anand2532/nRF9161-DEV-BOARD/reports/PASS30Z_SUMMARY.md

# PASS30Z_SUMMARY — RF Class C only

**Timestamp:** 2026-09-23 13:23 IST
**Decision:** **KEEP**
**Phase:** COMPLETE_KEEP

## DRC

| | unconnected | shorting | clearance | crossing |
| --- | ---: | ---: | ---: | ---: |
| Before | 67 | 0 | 0 | 0 |
| After | 64 | 0 | 0 | 0 |

**Gate:** clean=True; unconnected 67→64; closed={'ANT_FIT': True, 'AUX': True, 'AUX_FIT': True}; protect=True

## Class C (ANT_FIT / AUX / AUX_FIT)

| Net | Before open? | After open? | Closed? |
| --- | --- | --- | --- |
| ANT_FIT | True | False | True |
| AUX | True | False | True |
| AUX_FIT | True | False | True |

## Final XY (C22/C23/C24)

| Ref | Final XY | Stub len (mm) | GND via |
| --- | --- | --- | --- |
| C22 | [17.5, 31.75] | 0.883 | [17.5, 32.23] |
| C23 | [24.8, 34.0] | 1.0 | [25.98, 34.0] |
| C24 | [15.0, 31.8] | 1.2 | [16.18, 31.8] |

## Protect checklist

```
{
  "stage_a": {
    "VDD_nRF_via_north": true,
    "VDD2_vias": 2,
    "VDD2_present": true
  },
  "p015_west_tracks": 21,
  "U1": [
    36.0,
    32.0
  ],
  "J13": [
    64.0,
    76.0
  ],
  "J10": [
    116.0,
    28.0
  ],
  "J11": [
    116.0,
    46.0
  ],
  "L1": [
    22.0,
    32.0
  ],
  "L2": [
    20.0,
    33.0
  ],
  "TP1": [
    12.0,
    33.0
  ],
  "J2": [
    8.0,
    32.0
  ],
  "J3": [
    8.0,
    40.0
  ],
  "U3": [
    26.5,
    47.0
  ],
  "FB5": [
    23.8,
    47.65
  ],
  "C27": [
    22.0,
    35.0
  ],
  "L4": [
    18.0,
    38.0
  ],
  "ok": true,
  "reasons": []
}
```

## Notes

Removed 3 old island stubs. Targets per RF_STUB_DNP_PLAN. Collisions: []

**Backup:** `/workspace/kicad-projects/nRF9161-DEV-BOARD/.mcp-backups/pass30z-rf-class-c/pre-edit.kicad_pcb`
**Script:** `scripts/final_pass30z.py`
**DRC:** `reports/DRC_PASS30Z_BEFORE.json`, `reports/DRC_PASS30Z_AFTER.json`
