anand2532/nRF9161-DEV-BOARD/docs/PCB_LAYOUT_REVIEW.md

# PCB Layout Review — nRF9161-DEV-BOARD

**Role:** PCB Layout Engineer  
**Working path:** `/workspace/kicad-projects/nRF9161-DEV-BOARD`  
**Review date:** 2026-09-30 12:43 IST (Asia/Calcutta) — pass30ax P0.16 KEEP (6-seg In1.Cu east skirt, no new via, foreign 0.21 mm, POWER 0.3378 mm; unc 60→59; P0.16 opens 1→0; GND islands 12→12 waived). Prior: 2026-09-30 11:27 IST (Asia/Calcutta) — pass30at P0.30 leftover NO-ROUTE (U1.88 via island to locked pass30as track 64.776 mm > 25 mm; no copper; unc 60). Prior: 2026-09-30 11:23 IST (Asia/Calcutta) — pass30as P0.30 KEEP (8-seg F.Cu+B.Cu jog, one via (112.40, 46.40), foreign 0.29 mm, POWER 0.7 mm; unc 61→60; P0.30 opens 2→1; GND islands 12→12 waived). Prior: 2026-09-30 11:07 IST (Asia/Calcutta) — pass30ar NO-ROUTE (P0.31 U1.89 to locked pass30aq track 66.737 mm > 25 mm; no copper; unc 61). Prior: 2026-09-30 11:01 IST (Asia/Calcutta) — pass30aq P0.31 KEEP (6-seg F.Cu jog around P0.22/P0.04/VDD_GPIO/J14, no via, foreign 0.23 mm, POWER 0.245 mm; unc 62→61; P0.31 opens 2→1; GND islands 12→12 waived). Prior: 2026-09-30 10:47 IST (Asia/Calcutta) — pass30ap VDD_GPIO last open KEEP (8-seg F.Cu jog around ENABLE/SIM_CLK/P0.20, no new via, POWER clearance 2.2373 mm; unc 63→62; VDD_GPIO opens 1→0; GND islands 12→12 waived). Prior: 2026-09-30 10:37 IST (Asia/Calcutta) — pass30ao NO-ROUTE (remaining VDD_GPIO 27.034 mm > 25 mm; shortest other `P0.31` 29.078 mm > 20 mm; unc 63→63, no copper). Prior: 2026-09-30 10:33 IST (Asia/Calcutta) — pass30an VDD_GPIO east KEEP (y=7.050, D3.1 clearance 0.385 mm; unc 63→63; VDD_GPIO opens 2→1; GND islands 11→12 waived). Prior: 2026-09-30 10:28 IST (Asia/Calcutta) — pass30am VDD_GPIO east REVERT (attempt mid: VDD_GPIO opens 2→1, clearance 1 vs D3.1 VIN, GND islands 11→12 waived; restored unc 63→63). Prior: pass30al COEX0 KEEP (unc 64→63; COEX0 opens 1→0; GND islands 11→11). Prior: pass30ak VDD_GPIO shove KEEP (unc headline was 64; VDD_GPIO opens 3→2; GND island 10→11 waived). Prior: pass30aj same geometry REVERT; pass30ac Package A REVERTED; SE column FROZEN (pass30z keep)
**Overall:** **NOT FABRICATION-READY** — connectivity hard gate open  
**Gerbers:** **Do not generate** until `unconnected_items = 0` and DFM checklist is green  

Cross-refs: `docs/FAB_READY_CHECKLIST.md` (DFM gate **RED**), `docs/FAB_STACKUP_NOTES.md`, `docs/PM_STATUS.md`, `reports/FINAL_FAB_RELEASE.md`, `reports/DRC_AFTER_CONNECT.json`, `reports/UNCONNECTED_AFTER_FINAL.csv`.

---

## 1. Current connectivity status

**2026-09-30 pass30ax:** P0.16 **KEEP**. Unconnected 60→59. P0.16 opens 1→0. See `reports/PASS30AX_SUMMARY.md`.

**2026-09-30 12:27 IST — pass30aw no-copper census.** U1-open pads 37, can exit 31, trapped 6 (U1.24 included). Board file not modified. See `reports/PASS30AW_SHORTLIST.md`.

| Metric | Count | Source |
| --- | --- | --- |
| **unconnected_items** | **59** | `reports/DRC_PASS30AX_AFTER.json`. pass30ax KEEP: P0.16 opens 1→0. Prior live count was 60 (`DRC_PASS30AS_AFTER.json`). pass30at NO-ROUTE (P0.30 leftover 64.776 mm > 25 mm, no copper). Prior pass30as KEEP: P0.30 opens 2→1. GND islands 12 (waived). foreign 0.29 mm, POWER 0.7 mm. Prior pass30ar NO-ROUTE
| **shorting_items** | **0** | `reports/DRC_PASS30AS_AFTER.json` |
| **clearance** | **0** | Pass30 after (was 6 at baseline; zone refill cleared via/zone hits) |
| **hole_clearance** | **0** | Same |
| via_dangling | **78** | `DRC_PASS30F_AFTER.json` |
| drill_out_of_range | **0** | Pass30 before/after — P0.02 & nRESET already ≥0.50/0.30 |
| via_diameter | **0** | Same |
| track_dangling | 13 | Same JSON (includes load-bearing P0.15 west-wrap stubs) |
| silk_overlap / silk_over_copper | 147 / 36 | Cosmetics — after copper freeze |
| Live copper | ~780 segments, ~250 vias | Live after pass30 |

### Count reconciliation (do not mix eras)

| Report | unconnected | Notes |
| --- | --- | --- |
| `reports/DRC_SUMMARY.txt` | 116 | Older summary — **superseded** |
| `reports/DRC_BEFORE_FINAL.json` | 120 | Pre-final pass |
| `reports/DRC_final.json` / `FINAL_DESIGN_REVIEW.md` | 104 | Mid campaign |
| `reports/DRC_AFTER_CONNECT_FULL.json` | 98 | Intermediate |
| **`DRC_PASS30W_AFTER.json`** | **67** | **Authoritative after pass30w** (STOP two fails; Option E handoff; pass30u keep intact) |
| `DRC_PASS30V_AFTER.json` | 67 | Prior — STOP two fails; no keep |
| `DRC_PASS30U_AFTER.json` | 67 | Prior — P0.19 J18↔J13; Stage A+pass30i–30t+P0.22 kept |
| `DRC_PASS30T_AFTER.json` | 68 | Prior — VDD_GPIO J16↔J17; P0.11/10/17 probes reverted |
| `DRC_PASS30M_AFTER.json` | 74 | Prior — nRESET probed+reverted; Stage A+pass30i–30l kept |
| `DRC_PASS30L_AFTER.json` | 74 | Prior — SWDCLK closed; nRESET reverted |
| `DRC_PASS30K_AFTER.json` | 75 | Prior — VIN_F closed; Stage A+pass30i/30j kept |
| `DRC_PASS30J_AFTER.json` | 76 | Prior — P0.08→J12.9 stitch |
| `DRC_PASS30I_AFTER.json` | 77 | Prior — P0.08 U1↔SW3/R14 only |

**Pass delta (pass30ax):** P0.16 U1.26↔J18.4, **KEEP**. Straight line not used (crosses the SiP; GND via (42.0, 32.0) at about -0.349 mm). F.Cu and B.Cu from the existing via (40.70, 20.80) are walled north of the body, so the skirt is six 0.18 mm In1.Cu segments east of the fab body: (40.70, 20.80)→(45.55, 20.80)→(45.55, 27.40)→(44.60, 27.40)→(44.60, 60.40)→(45.62, 60.40)→(45.62, 61.10). No new via. Pre-add foreign 0.21 mm (P0.06 via), POWER 0.3378 mm (VDD2 via). P0.16 opens 1→0. Unconnected 60→59. short/clearance/crossing/hole 0/0/0/0. hole_to_hole 1→1. GND islands 12→12 (waived). Stub, P0.15, P0.19, P0.30, P0.31, P0.22, P0.04, VDD_GPIO, COEX0, Class C, DEC0, P0.10/P0.12, Stage-A VDD2, SIM walls not ripped. No header or U1 move. No y=44.60 pocket. x>24.2. No P0.17. No Gerbers. Details: `reports/PASS30AX_SUMMARY.md`.

**Pass delta (pass30aw):** no-copper census of U1 pads on non-GND opens. 37 such pads: **31 can exit** the fab body (x 28.0–44.0, y 26.75–37.25), **6 trapped**, **0 trapped-by-keepout**. Shortest exitable is `P0.16` 34.259 mm (U1.26 stub via 40.70, 20.80). Trapped: U1.24 P0.14 via-row 0.400 mm / sideways 0.200 mm; U1.29 P0.18, U1.96 P0.01, U1.87 P0.29, U1.92 COEX1 the same 0.400/0.200 pinch; U1.59 MIPI_SDATA via-row 0 (MIPI_SCLK via straddles the axis). U1.88 P0.30 classified exit by its existing via (36.25, 41.10); U1.89 P0.31 classified exit by a 0.900 mm via-row (P0.30 via to COEX2 via). Neither was routed. Board sha256 unchanged `3f209b08…ff005`. Unconnected stays 60. No Gerbers. Details: `reports/PASS30AW_SUMMARY.md`, `reports/PASS30AW_SHORTLIST.md`.

**Pass delta (pass30at):** P0.30 leftover U1.88↔locked pass30as track, **NO-ROUTE**. Copper-edge gap 64.776 mm on F.Cu, via@(36.25, 41.10) ring edge (36.549, 41.124) to the west edge of F.Cu (101.20, 46.40)–(112.40, 46.40) at (101.110, 46.393). U1.88 pad-edge to that track is 65.303 mm. Over the 25 mm cap, so no jog. Straight 0.18 mm chord hits 16 foreign nets (nearest SIM_1V8 -0.290 mm; also VDD2, VDD_GPIO, locked COEX0 and SIM_CLK_C). Unconnected stays 60. Locked pass30as run not ripped. P0.31 leftover not retried. P0.14 not started. No Gerbers. Details: `reports/PASS30AT_SUMMARY.md`, `reports/PASS30AT_SHORTLIST.md`.

**Pass delta (pass30as):** P0.30 J13.15↔J11.1, **KEEP**. Straight line not used (VDD_GPIO, P0.04, locked P0.31, GND J15.6). Four 0.18 mm F.Cu segments to via (112.40, 46.40), four 0.18 mm B.Cu segments along the east gutter at y=45.00 / x=117.60 into J11.1, off the P0.31 landing. Pre-Add foreign clearance 0.29 mm (need 0.15), POWER/VIN 0.7 mm (need 0.20). P0.30 opens 2→1. Headline unconnected 61→60. short/clearance/crossing/hole_clearance 0/0/0/0. hole_to_hole 1→1. GND islands 12→12 (waived). Locked P0.31, VDD_GPIO, P0.22, P0.04, COEX0, DEC0, P0.10/P0.12 not ripped. No U1/header move. No y=44.60 pocket. x>24.2. No P0.14. No Gerbers. Details: `reports/PASS30AS_SUMMARY.md`.

**Pass delta (pass30ar):** P0.31 leftover U1.89↔pass30aq track, **NO-ROUTE**. Pad-edge gap 66.737 mm on F.Cu, (36.900, 37.614) pad U1.89 to (102.961, 47.087) on F.Cu (103.05, 47.10)–(106.70, 47.10). Over the 25 mm cap, so no jog. Straight 0.18 mm chord hits 17 foreign nets (nearest SIM_CLK via -0.301 mm). Unconnected stays 61. Locked pass30aq run not ripped. P0.30 not started. No Gerbers. Details: `reports/PASS30AR_SUMMARY.md`, `reports/PASS30AR_SHORTLIST.md`.

**Pass delta (pass30aq):** P0.31 J13.16↔J11.2, **KEEP**. Straight line not used (P0.22, GND via (110, 50), VDD_GPIO, P0.04). Six 0.18 mm F.Cu segments, no via: west of J14, north of J14.1, y=50.62 north of the VDD_GPIO trunk and south of the P0.04 corner, into J11.2. Pre-Add foreign clearance 0.23 mm (need 0.15), POWER/VIN 0.245 mm (need 0.20). P0.31 opens 2→1. Headline unconnected 62→61. short/clearance/crossing/hole_clearance 0/0/0/0. hole_to_hole 1→1. GND islands 12→12 (waived). Locked VDD_GPIO (pass30ap run, y=7.050, U1.12), P0.22, P0.04, COEX0, DEC0, P0.10/P0.12 not ripped. No U1/header move. No y=44.60 pocket. x>24.2. No P0.30. No Gerbers. Details: `reports/PASS30AQ_SUMMARY.md`.

**Pass delta (pass30ap):** last VDD_GPIO open, **KEEP**. Straight line not used (ENABLE, SIM_CLK, P0.20). Eight 0.18 mm F.Cu segments from the existing via (76.4375, 39.050) around those trunks, west of P0.20 at x=54.438, into J18.9. No new via. Pre-Add POWER/VIN clearance 2.2373 mm (need 0.20). VDD_GPIO opens 1→0. Headline unconnected 63→62. short/clearance/crossing/hole_clearance 0/0/0/0. hole_to_hole 1→1. GND islands 12→12 (waived). Locked y=7.050 run, U1.12 polyline, COEX0, DEC0 bridge, P0.10/P0.12 not ripped. No U1/header move. No y=44.60 pocket. x>24.2. No Gerbers. Details: `reports/PASS30AP_SUMMARY.md`.

**Pass delta (pass30an):** VDD_GPIO east island replay of pass30am, **KEEP**. Same corners except the horizontal moved north off y=7.300. Pre-commit measured clearance of the 0.18 mm horizontal to pad D3.1 [VIN] (75.213, 8.000) is 0.385 mm at y=7.050 (requirement 0.20 mm; y=6.800 not used). Segments: (71.300, 8.000)→(71.300, 7.050)→(77.300, 7.050)→(81.500, 13.500)→(86.510, 26.000). VDD_GPIO opens 2→1. Headline unconnected 63→63. short/clearance/crossing/hole_clearance 0/0/0/0. hole_to_hole 1→1. GND islands 11→12 (waived). Locked U1.12 polyline, COEX0, DEC0 bridge, P0.10/P0.12 x=47.0 not ripped. No U1/header move. No y=44.60 pocket. x>24.2. No Gerbers. Details: `reports/PASS30AN_SUMMARY.md`.

**Pass delta (pass30am):** VDD_GPIO east island, **REVERT** (one attempt). Shortest remaining non-GND gap 17.626 mm (F.Cu y=32 trunk ↔ B.Cu x=70 riser). Straight B.Cu hits VIN_F / P0.08 / COEX2; COEX2 at x=72 walls a B.Cu hop. Four 0.18 mm F.Cu segments, no via: (71.300, 8.000)→(71.300, 7.300)→(77.300, 7.300)→(81.500, 13.500)→(86.510, 26.000), from the existing via (71.300, 8.000) onto the R14 junction. Mid DRC: VDD_GPIO opens 2→1, short/crossing/hole_clearance 0, hole_to_hole 1→1, GND islands 11→12 (waived) but clearance=1 — POWER netclass 0.150 mm vs pad D3.1 [VIN] (75.213, 8.000), actual 0.135 mm on the y=7.300 horizontal. Full restore. Final unconnected 63→63, short/clearance/crossing/hole_clearance 0/0/0/0. Locked U1.12 polyline, COEX0, DEC0 bridge, P0.10/P0.12 x=47.0 not ripped. No U1/header move. No y=44.60 pocket. x>24.2. No second attempt. No Gerbers. Details: `reports/PASS30AM_SUMMARY.md`.

**Pass delta (pass30al):** COEX0 landing, **KEEP**. Straight F.Cu from the R4 via island (29.810, 22.000) to the y=38 run hits no-net U1.51 and U1.73; 0.50 mm pad pitch cannot be threaded, and a west F.Cu jog east of x=24.2 crosses MAGPIO/MIPI and ANT/AUX/GPS (AUX reaches x=20.485). One 0.6/0.3 via at (37.000, 30.500). Six 0.18 mm segments: B (31.110, 22.000)→(32.250, 22.000)→(32.250, 30.500)→(37.000, 30.500), F (37.000, 30.500)→(37.000, 35.900)→(38.750, 35.900)→(38.750, 37.250) onto U1.93 (same island as the y=38 run). COEX0 opens 1→0. Headline unconnected 64→63. short/clearance/crossing/hole_clearance 0/0/0/0. hole_to_hole 1→1. GND islands 11→11 (waived). No non-GND net gained an open. P0.15 still 42. VDD_GPIO polyline, DEC0 B.Cu bridge, P0.10/P0.12 x=47.0 not ripped. No U1/header move. No y=44.60 pocket. No Gerbers. Details: `reports/PASS30AL_SUMMARY.md`.

**Pass delta (pass30ak):** Replay of the pass30aj shove, **KEEP**. Same 0.18 mm F.Cu polyline (40.170, 19.126)→(40.170, 20.200)→(45.900, 20.200)→(45.900, 25.400)→(47.550, 25.400)→(47.550, 31.500)→(44.000, 31.500). Shoved only P0.12 and P0.10 (dangling vias x=47.4→47.0) and DEC0 (F.Cu gap near x=47.55 bridged on B.Cu). P0.08 and P0.11 not shoved. P0.15 segments 42→42. New gate waives the extra F.Cu GND zone island. short/clearance/crossing/hole_clearance 0. VDD_GPIO opens 3→2. No non-GND net gained an open. Headline unconnected 64→64 because GND islands 10→11. No U1/header move. No COEX0. No Gerbers. Details: `reports/PASS30AK_SUMMARY.md`.

**Pass delta (pass30ai):** VDD_GPIO one jog, **REVERT**. Live via island VDD_GPIO F.Cu @(40.170, 19.126) dia 0.8/0.4 → U1.12 (44.000, 31.500). Three 0.18 mm F.Cu segments: (40.170,19.126)→(45.500,20.150)→(45.500,26.050)→(44.000,31.500). Segments 1–2 clear P0.16 and the P0.15 keep. Landing segment tracks_crossing=8 (P0.08, P0.10, P0.11, P0.12, DEC0×4). short/clearance/hole 0. Unconnected 64→64 (VDD_GPIO 3→2 offset by GND zone islands 10→11). No via. Full restore to pre-edit. No Gerbers. Details: `reports/PASS30AI_SUMMARY.md`.

**Pass delta (pass30ah):** **NO ROUTE.** Shortest real (non-GND, non-protected-keep) island gap is `VDD_GPIO` **12.305 mm** F.Cu via@(40.17,19.13) ↔ pad U1.12 — over the 12 mm gate, and the straight line shorts the P0.15 keep plus P0.16. Zero gaps ≤ 12 mm, so no track and no via. Unconnected 64→64. short/clr/cross 0/0/0 (baseline). GND zone islands ignored. SIM walls, Class C, Stage-A VDD2, P0.22/P0.19/P0.04/P0.06/P0.01 and the y=44.60 pocket untouched. No Gerbers. Details: `reports/PASS30AH_SUMMARY.md`, shortlist `reports/PASS30AH_SHORTLIST.md`.

**Pass delta (pass30ag):** Corridor probe `SIM_RST` **REVERT**. SIM_RST_C already continuous. In-corridor B track did not join any open island (pocket sealed by SIM_IO_C @x78.60 and SIM_CLK_C @x78.95 / x97.85). Unconnected 64→64. short/clr/cross 0/0/0. Corridor still free. No Gerbers. Details: `reports/PASS30AG_SUMMARY.md`.

Live `kicad-cli` 9.0.2 DRC was re-run for pass30c (`reports/DRC_PASS30C_BEFORE.json` / `reports/DRC_PASS30C_AFTER.json`). On-disk `fab/gerbers/` CreationDate **2026-09-16** remains **stale** and must not be used for fab (DFM checklist §5).

**Pass delta (pass30ac):** Package A_SE_duals EXECUTE (J16+J9+J17; **excl J12**). Preferred west −2.54 → (105.46,8)/(113.46,8)/(105.46,26) mid dirty shorting=7 clr=1 cross=4 (P0.01 B@y15.2 × J17/J16; P0.04/P0.06 × VDD_GPIO/J9). Alt Y once J16/J9 south +2.54 / J17 north −2.0 also dirty shorting=11 clr=5 cross=7 unc 64→68. **FULL PACKAGE REVERT** to pass30z keep. Landing: **none**. Final XY unchanged. Before/After unconnected: 64/64 · shorting/clearance/crossing 0. Class C + Stage A + SE column frozen + J12 unmoved. No Gerbers. Details: `reports/PASS30AC_SUMMARY.json` (+ MD).

**Pass delta (pass30ad):** B'' PROPOSALS ONLY (no execute). J10/J11-only west: **no** safe ≤3 mm clearing P0.22 via@(112.5,32.5)/(114.7,29.9) + P0.04 F (even −0.5 fails; 113.46 banned). Optional J13 west-only ≤2 mm toward x=62 statically clears P0.01/P0.08 forest but does not unlock SE duals alone. **Recommendation: LEAVE SE COLUMN FROZEN** until copper pre-clear + PM OK. Artifacts: `reports/PASS30AD_B_DOUBLE_PRIME_PROPOSALS.md` (+ JSON).

**Pass delta (pass30y):** Package B ONLY atomic place+reattach (J13+J10+J11). Live start XY confirmed J13(64,76)/J10(116,28)/J11(116,46). Preferred J13→(64,78.5)+J10/J11→(113.46,*) mid-DRC dirty shorting=11 clearance=3 crossing=7 hole_clearance=4 (edge-class: P0.01/P0.04/P0.06 south highways @y≈78.5–79.2 + J10 west vs P0.22 via@112.5). Alt once J13→(67,76)+same J10/J11 also dirty shorting=16 clearance=3 crossing=4 hole_clearance=4 (J10.3↔P0.22 via; J13.6↔P0.01 via; VDD_GPIO reattach diagonals). **FULL PACKAGE REVERT** to pass30u keep. J13 landing kept: **none**. Final XY unchanged. Before/After unconnected: 67/67 · shorting/clearance/crossing 0. Stage A + P0.15 west + P0.22/P0.19 keeps intact. No Package A/C/D. No U1 move. No Gerbers. Details: `reports/PASS30Y_SUMMARY.json` (+ MD).

**Pass delta (pass30x):** PLACEMENT PROPOSALS ONLY — no footprint moves, no copper, no Gerbers. Measured live XY J8–J17 + U1. Packages: (A) SE duals J9/J12/J16/J17 for P0.05/07/09–12/17; (B) SE column J10/J11/J13 for P0.18–31 — J13 preferred (64,78.5) / alt (67,76); **do not repeat failed (64,73)** vs P0.08 vias @65.2; (C) West long-haul J14/J15 for MAGPIO/MIPI/COEX1; (D) VDD_GPIO U1.12 note only — **no U1 move without later explicit OK**. PM override: waive **only** GND×10; MUST-FIX ANT_FIT/AUX/AUX_FIT (RF Class C DNP place-later); P0.19/P0.22 leftover ratsnests are real GPIO opens (Package B helps). Hard gate still unconnected→0. Artifacts: `reports/PASS30X_PLACEMENT_PROPOSALS.md` (+ JSON).

**Pass delta (pass30w):** Ordered VDD_GPIO low-risk island joins only (NEW geometries). U1.12 NW F@y34.5 + B col@x35.5 F-hops — dirty shorting=12 clearance=11 (hit P0.22/P0.21 via forest @x35.25/35.75). Mid via(87.81,26)→TP10 F-hops — dirty shorting=2 clearance=1 crossing=3 (VIN_FILT). **STOP** two consecutive dirty fails; SIM_*/COEX1/MAGPIO long-haul (~40–80 mm) **not** short-stub class — deferred. SE dual GPIO thrash skipped. **Nothing kept** → Option E matrix `reports/REMAINING_OPENS_MATRIX.md` (+ JSON). **Before/After unconnected:** 67/67 · shorting/clearance/crossing 0. P0.15 west preserved (21 segs). Stage A + P0.22 + P0.19 keep. No placement. No Gerbers. No further copper pass. Details: `reports/PASS30W_SUMMARY.json`.

**Pass delta (pass30v):** Ordered duals P0.05→P0.07 NEW bottom-F highways — both dirty (shorting/clearance/crossing); atomic revert; **STOP** two consecutive fails. P0.09/12/18/21/23/24 and VDD_GPIO not attempted in ordered run. Post-stop probes (all reverted): SE J13↔J10 blocked by VDD_GPIO dual H@y51.08 + P0.22@x109.2 + J17@x108 corridor squeeze; VDD mid@x78 blocked by P0.08/COEX2/P0.15/VIN_F. **Before/After unconnected:** 67/67 · shorting/clearance/crossing 0. P0.15 west preserved (21 segs). Stage A + P0.22 + P0.19 keep. No placement. No Gerbers. Details: `reports/PASS30V_SUMMARY.json`.

**Pass delta (pass30u):** NEW corridors only (avoid pass30t P0.11/P0.10/P0.17 geometries). P0.19 J18.7↔J13.4 B@y64 + F-hop over P0.08@x65.2 — **KEPT**. COEX0 B west-col dirty (shorting=6 clearance=4) — reverted. P0.30 J13↔J11 east dirty (clearance=1 crossing=7) — reverted. **STOP** after two consecutive fails; VDD_GPIO mid not attempted. P0.31 skipped. **Before/After unconnected:** 68/67 · shorting/clearance/crossing 0. P0.15 west preserved (21 segs). Stage A + P0.22 keep. No placement. No Gerbers. Details: `reports/PASS30U_SUMMARY.json`.

**Pass delta (pass30c):** netlist sync + U3.VIN + U3.ON closed. **Before unconnected:** 80 · **After unconnected:** 78 · **Nets closed:** VDD_GPIO (U3.1), COEX0 (U3.3). Class F deferred. shorting/clearance=0. P0.15 wrap preserved.

**Pass delta (pass30e):** Aggressive Class F corridor clear (PM-approved rip list). **Before/After unconnected:** 78/78 · **shorting/clearance:** 0/0 · **Nets closed:** none. ENABLE restore was the failing link. All trial copper reverted. Details: `reports/PASS30E_SUMMARY.json`.

**Pass delta (pass30f):** ONE atomic VIN_FILT co-route. **Before/After unconnected:** 78/78 · **shorting/clearance:** 0/0 · **Nets closed:** `VIN_FILT` (offset by Class-E GND zone islands 9→10). Ripped+restored in same transaction: VDD_GPIO north U@y9, P0.15 F via-bridge (vias@51/60,y16.5 + F@19.5), ENABLE F via-bridge, VDD2_MID south jog@y17.8. P0.08 probe after approved rips still blocked (VDD_nRF via@69.3,30 + via forest) — no live trial copper kept. STOP per still-78 rule; placement-move list for Hardware PM. Details: `reports/PASS30F_SUMMARY.json`.

**Pass delta (pass30i):** ONE atomic P0.08 + ENABLE/COEX2 co-route (Stage A kept; no placement). Ripped ENABLE V@62.5 / V@76.8 / H@y28 + COEX2 V@72; placed P0.08 B@y30.25; restored with F via-bridges (ENABLE@x62.5 ys/yn=29.6/30.9, COEX2@x72 same, ENABLE east F-hop to x=79.2). **Before/After unconnected:** 78/77 · shorting/clearance/crossing 0. Closed P0.08 U1↔SW3/R14; J12.9 still open. P0.15 west preserved. Details: `reports/PASS30I_SUMMARY.json`.

**Pass delta (pass30j):** ONE honest cycle — stitch P0.08 island→J12.9. B column @x=65.2 with F via-hops over COEX2/COEX0/P0.18+P0.17; rip+restore P0.15 bottom H (wide F-bridge 61.5–68.5 @y77.45) + P0.01 (final F-bridge 24.5–27.2 @y78.5 + column U-jog F@y74.5); B H@y79 → via(26.32,78) → F to J12.9. **Before/After unconnected:** 77/76 · shorting/clearance/crossing 0. P0.15 west wrap preserved (21 segs). VIN_F/SWDCLK skipped (not cheap). Details: `reports/PASS30J_SUMMARY.json`.

**Pass delta (pass30o):** P0.02 atomic close (west col x=27.5, B@y4.5, east col x=89). Preflight rip: VDD_GPIO V@48.05 (U-jog west), P0.01 H@15.2 (F-hop 88.2–89.8), P0.15 east H@7.2 (F-hop 88.2–89.8). **Before/After unconnected:** 73/72 · shorting/clearance/crossing 0. P0.15 west wrap preserved. Stage A + pass30i–30n kept. No Gerbers. Details: `reports/PASS30O_SUMMARY.json`.

**Pass delta (pass30n):** ONE atomic nRESET co-route (F@y10.8 under VDD_nRF/JP1). Preflight rip (3): P0.15 (72.0,15.35)→(72.0,7.2), COEX2 (72.0,24.6)→(105.1,24.6), P0.01 (86.14,15.2)→(105.55,15.2). nRESET **KEPT** B@y12.6 + F clearance hop + F-hop 69–71.5; COEX2/P0.01/P0.15 east co-restored. **Before/After unconnected:** 74/73 · shorting/clearance/crossing 0. P0.02 skipped (no free corridor). Stage A + pass30i–30l kept. P0.15 west wrap preserved. No Gerbers. Details: `reports/PASS30N_SUMMARY.json`.

**Pass delta (pass30m):** ONE atomic nRESET co-route. Preflight rip list (1 seg) recorded before copper edit: P0.15 B.Cu (72.0,15.35)→(72.0,7.2). Ripped → routed nRESET B@y12.6 + F-hop 69.0–71.5 over VDD_GPIO/VIN_F → P0.15 F-bridge restore → mid DRC clearance=1 crossing=2 (shorting=0) → **atomic revert**. Colliding copper: nRESET×COEX2, nRESET×P0.01 on B; clearance vs VDD_nRF via@(57.95,12.0). P0.02 not attempted. **Before/After unconnected:** 74/74 · shorting/clearance/crossing 0. Stage A + pass30i–30l kept. P0.15 west wrap preserved. No Gerbers. Details: `reports/PASS30M_SUMMARY.json`.

**Pass delta (pass30l):** ONE honest Class-F cycle (SWDCLK→nRESET→P0.02; option C scan). SWDCLK mixed F/B west column x=34.2 + F-hop over VDD_GPIO H@19.13 + F north band y=1.5 around J8.3 into via@(53.65,4.73) — **closed**. nRESET @y12.6 corridor probed then **reverted** (shorting/clearance/crossing). P0.02 skipped. Option C: no cheap non-RF/U3 stub. **Before/After unconnected:** 75/74 · shorting/clearance/crossing 0. P0.15 west wrap preserved (21 segs). Stage A + pass30i–30k kept. No J8 move. No Gerbers. Details: `reports/PASS30L_SUMMARY.json`.

**Pass delta (pass30k):** ONE honest Class-F cycle (VIN_F→SWDCLK→nRESET→P0.02). VIN_F B@y11 + F-hop over VDD_GPIO@x70 + B to FB4 island; P0.15 east H@y15.35 F-bridged (69.3–72.0). SWDCLK/nRESET probed then left (restore not DRC-clean in one attempt); P0.02 skipped — STOP. **Before/After unconnected:** 76/75 · shorting/clearance/crossing 0. P0.15 west wrap preserved (21 segs). Stage A + pass30i/30j kept. Details: `reports/PASS30K_SUMMARY.json`.

**Pass delta (pass30h):** ONE honest cycle. Stage A KEPT (VDD2 B walls→via-bridge @x=58; VDD_nRF via (69.3,30)→(69.3,31.5) north). P0.08 probe CLEAR @y=30.25 after ENABLE/COEX2 rip but restore re-crosses / jog hits VDD_GPIO — **reverted**. Stage B placement REVERTED (shorting=5; C6.1@x=48.68 DEC0). **Before/After unconnected:** 78/78 · shorting/clearance/crossing 0. Details: `reports/PASS30H_SUMMARY.json`.

---

## 2. Stackup note

### Present on PCB (copper / planes)

| Layer | Role on disk |
| --- | --- |
| F.Cu | Components, RF microstrip, short digital; GND pour zone present |
| In1.Cu | **GND** plane zone |
| In2.Cu | **VDD_nRF** plane zone |
| B.Cu | GPIO / returns; GND pour zone |
| Board thickness | **1.6 mm** (`(thickness 1.6)` in PCB setup) |
| Outline | 120 × 80 mm |

RF keepout zones (net 0 / empty name, F.Cu+B.Cu) exist in the PCB (west matching / U.FL region). Coordinate keepout changes with **RF Power Engineer via Hardware PM** — do not move LTE/GNSS/AUX 50 Ω trunks or matching without evidence.

### Dielectric / fab stackup — **NOT LOCKED (Hardware PM / Anand)**

Authoritative open questions are in **`docs/FAB_STACKUP_NOTES.md`** (2026-09-23): README assumes ~0.12 mm L1↔L2 prepreg for 0.20 mm `RF_50OHM`, while stale `fab/gerbers/nRF9161-DEV-BOARD-job.gbrjob` lists ~0.48 mm FR4 between Cu pairs and `Finish: None`. Layout must **not** treat either as manufacturer truth.

KiCad board setup has thickness **1.6 mm** and copper roles above, but **no** locked MaterialStackup coupon.

#### Working layout assumption (explicitly pending Anand answers in FAB_STACKUP_NOTES)

Until Anand confirms stack/order, L1–L2 H/Er, finish, and impedance coupon, Layout continues to treat the **README RF assumption** as the working geometry only:

| Layer | Working assumption | Use |
| --- | --- | --- |
| L1 F.Cu | 1 oz | Signals + RF microstrip |
| Prepreg L1–L2 | ~0.12 mm, εr ≈ 4.2 (JLC-like) — **UNCONFIRMED** | RF reference height |
| L2 In1.Cu | 1 oz | Solid **GND** under 50 Ω |
| Core | ~1.2 mm | |
| L3 In2.Cu | 1 oz | **VDD_nRF** pour |
| Prepreg L3–L4 | ~0.12 mm | |
| L4 B.Cu | 1 oz | Digital + GND pour |

**50 Ω working width:** ≈ **0.20 mm** on F.Cu over In1 GND — **recalculate after fab coupon**. Do not regenerate impedance-controlled Gerbers until unconnected=0 **and** stackup answers land.

**Surface finish:** unset (`Finish=None`) — PM/fab decision.

**Status for DFM §1:** remains **FAIL** until Anand closes `docs/FAB_STACKUP_NOTES.md`.

---

## 3. Remaining unconnected classes

Classification from `reports/UNCONNECTED_AFTER_FINAL.csv` (80 rows; matches `FINAL_FAB_RELEASE.md` narrative).

| Class | Count | Meaning |
| --- | --- | --- |
| **A** | **55** | U1 / fanout via / track ↔ header or island (GPIO, MAGPIO/MIPI/COEX, SIM, VDD_GPIO) |
| **E** | **9** | GND F.Cu zone-to-zone islands (dist 0.000 — zone fill / island merge) |
| **G** | **7** | Header duplicate branches (J13 ↔ J10/J11/J18 same-net copies) |
| **F** | **6** | F.Cu / mixed power & debug islands (VIN, nRESET, SWDCLK, P0.08) |
| **C** | **3** | DNP RF shunt stubs (ANT_FIT / AUX / AUX_FIT) — **do not rip 50 Ω trunks** |

### 3.1 Named walls (unchanged — load-bearing)

- **P0.15 west wrap (ROUTED, status OPEN count 0 in GPIO_FINAL):** U1 pad 25 @ (41.75, 26.75) → via **(41.75, 23.10)** → B.Cu courtyard snake x≈31.00–36.50, y≈22.50–59.20 into J18 / J12. **Do not delete.** Blocks naive P0.13–P0.18 U1→existing-B hops. East x=106 copper is fed from J18/J12 south stubs, not an independent U1 hop.
- **ENABLE vias @ (42.75, 41.10) and neighbors** — occupy south courtyard column needed for ADC exits; several ENABLE vias are also in the **via_dangling** set.
- **RF keepout west** ≈ (0, 20)–(24.2, 64) mm — MAGPIO/MIPI must jog **north of keepout**, not through matching.

### 3.2 Class F — power / debug opens (concrete)

| Net | Dist mm | Endpoints (approx) | Notes |
| --- | --- | --- | --- |
| VIN_FILT | — | closed in pass30f | B.Cu (55.35,13.3)→(51.9,13.3)→(51.9,21.9); restores held |
| VIN_F | 24.444 | (48.00, 12.60) ↔ (71.58, 19.06) | North power island |
| nRESET | 68.922 | B (101.68, 58.80) ↔ F (52.22, 10.80) | Long; also owns undersized via @ (45.68, 15.8) |
| SWDCLK | 26.202 | J8 stub (51.95, 4.73) ↔ U1 pad 33 (37.75, 26.75) | Debug critical |
| P0.08 | 32.730 / 49.281 | via/track islands ↔ J12.9 | USER button net |

### 3.3 Class A highlights — VIN / SIM / GPIO / west interfaces

**SIM (U1 → TPD3F303 / J7 side):**

| Net | Dist mm | U1 / island | Far end |
| --- | --- | --- | --- |
| SIM_CLK | 41.382 | U1 pad 46 (31.25, 26.75) | B.Cu track (68.14, 45.50) |
| SIM_IO | 51.975 | U1 pad 48 (30.25, 26.75) | F.Cu track (75.68, 52.00) |
| SIM_RST | 44.352 | U1 pad 43 (32.75, 26.75) | B.Cu track (71.68, 48.00) |
| SIM_1V8 | 46.507 | U1 pad 49 (29.75, 26.75) | F.Cu track (72.90, 44.10) |

**West MAGPIO / MIPI / COEX (U1 west edge ↔ J14/J15 @ x≈104):** MAGPIO0/1/2, MIPI_SCLK/SDATA/VIO, COEX0/1 — all still OPEN (~70–80 mm). Must skirt RF keepout north.

**ADC / south GPIO (blocked by P0.15 wrap + J18 PTH wall y≈60–65):** P0.13, P0.14, P0.16–P0.20 still OPEN U1↔J18/J12/J13. P0.15 itself is **ROUTED** via the wrap.

**East GPIO / SPI / I2C / UART copies:** many P0.05/07/09–12/21–31 U1↔J12/J13 opens; Class G adds J13↔J10/J11/J18 duplicate branches once primaries land.

**VDD_GPIO:** 5 open items (U1 pad 12 islands, header stubs, FB5).

**Near-miss stub:** P0.11 F.Cu track @ (48.62, 28.00) ↔ U1 pad 19 @ (44.00, 28.00) — **4.62 mm** (shortest Class A gap; courtyard congestion).

### 3.4 Class C — DNP RF shunts (coordinate with RF)

| Net | Dist mm | Notes |
| --- | --- | --- |
| ANT_FIT | 4.470 | C22 pad ↔ ANT_FIT track — short stub only |
| AUX | 17.355 | AUX track ↔ C23 |
| AUX_FIT | 23.000 | C24 ↔ AUX_FIT track |

Close with **short same-net stubs** or explicit NC policy — **never** by ripping L1/C21/C22 or GNSS trunks.

### 3.5 Class E — GND zone islands

Nine F.Cu GND zone-to-zone entries at (≈−0.05, −0.05). Likely fill / island merge after copper freeze + zone refill — not discrete signal routes.

### 3.6 DFM via issues to fold into the **same** routing pass (after connectivity P0)

From `reports/DRC_AFTER_CONNECT.json` + `docs/FAB_READY_CHECKLIST.md` §2:

| Issue | Count | Concrete |
| --- | --- | --- |
| **via_dangling** | **82** | Fanout vias connected on only one layer — nets include VDD_GPIO(7), VIN_F(6), ENABLE(4), VDD2(4), VIN_FILT(4), SIM_*, nRESET, P0.xx, MAGPIO1, MIPI_VIO, COEX0, … (45 unique nets). Completing B.Cu (or F.Cu) stubs on these vias is part of closing Class A/F, not a separate campaign after Gerbers. |
| **drill_out_of_range** | **2** | Via **P0.02** @ **(40.75, 43.5)** and via **nRESET** @ **(45.68, 15.8)** — hole **0.25 mm** &lt; min **0.30 mm** |
| **via_diameter** | **2** | **Same two vias** — diameter **0.45 mm** &lt; min **0.50 mm**. Upsize to project default **0.60 / 0.30** (or at least 0.50 / 0.30) when touching those nets. |

---

## 4. Prioritized fix plan

### P0 — Connectivity hard gate (`unconnected → 0`)

1. **Preserve P0.15 west wrap** and RF matching / keepouts — no rip-up without RF+PM sign-off.
2. **Close Class F power/debug islands** first where geometry is local: VIN_FILT (~10 mm F.Cu), then VIN_F, SWDCLK, nRESET (with via upsize), P0.08.
3. **SIM cluster** (SIM_CLK/IO/RST/1V8): private B.Cu or F.Cu paths U1 south/east → U4/J7 islands; avoid RF west box.
4. **ADC wall (P0.13–P0.14, P0.16–P0.20):** add staggered fanout vias **beyond** existing ring (1.15–2.1 mm), use **private** B.Cu columns (x≥64.6 east of J18, or west wrap corridor x≈25.1 **south of RF keepout**) — do not add another board-width y≈70 bus.
5. **Remaining GPIO / UART / SPI / I2C / I2S / PDM** U1→J12/J13 primaries, then Class G header duplicates.
6. **MAGPIO / MIPI / COEX:** north-of-keepout jog then east to J14/J15.
7. **VDD_GPIO** islands + FB5; Completing these also clears many dangling vias.
8. **Class C** DNP RF stubs / NC policy with RF Engineer.
9. **Class E** GND: refill F.Cu zones after copper edits; stitch islands if still reported.

### P1 — Fold into the **same** routing pass (DFM — do not defer to a post-Gerber cleanup)

Per Hardware PM / DFM (2026-09-23): after each connectivity move, **also**:

1. **Finish or remove** dangling vias on nets just closed (target: drive `via_dangling` down with unconnected). Prefer finishing B.Cu stubs over deleting load-bearing fanouts (ENABLE @ 42.75,41.10 is structural — connect or deliberately relocate with a plan).
2. **Fix undersized vias immediately when those nets are touched:**
   - P0.02 via (40.75, 43.5): resize ≥ **0.50 / 0.30** (prefer **0.60 / 0.30**)
   - nRESET via (45.68, 15.8): same
3. Re-check `track_dangling` on edited nets (expect some P0.15 stub warnings to remain until wrap topology is intentionally revised — do not “fix” by deleting wrap stubs).

### P2 — After unconnected = 0 (still before Gerbers)

1. Silk cleanup (147 overlap / 36 over copper).
2. Stackup + impedance coupon lock with Hardware PM / fab; update RF width if H/Er change.
3. Zone refill, lib_footprint_mismatch (3), EMS stencil notes.
4. Hand to DFM for green checklist → **only then** regenerate Gerbers / drill / IPC-356 / BOM / CPL / fab zip.

---

## 5. Explicit next routing pass proposal (ordered)

**Pass name:** `layout-pass30-connect` (proposed)  
**Tooling note:** Existing `scripts/*.py` assume `pcbnew` + `kicad-cli` (paths under `/home/anand/...`). Neither is available on this shared box right now — **do not blind-edit** the `.kicad_pcb` sexp without DRC. Next copper work should run where KiCad CLI works, with backup first.

| Step | Action | Target nets / geometry | Expected effect |
| --- | --- | --- | --- |
| 0 | Backup live PCB to `.mcp-backups/layout-pass30-<timestamp>/` | — | Safety |
| 1 | Baseline DRC JSON | record **before** `unconnected_items`, `via_dangling`, drill/via_diameter | PM ping numbers |
| 2 | F.Cu surgical: VIN_FILT island | (55.35,12.00)→(53.20,21.90), width power class | −1 F if clear |
| 3 | F.Cu surgical: VIN_F | (48.00,12.60)→(71.58,19.06) with jogs around north parts | −1 F |
| 4 | SWDCLK U1 pad 33 ↔ J8 stub | Prefer B.Cu under courtyard exit, avoid RF | −1 F |
| 5 | nRESET: connect islands **and** upsize via (45.68,15.8) to 0.60/0.30 | Long B↔F | −1 F + clear 1 drill/via_diameter |
| 6 | Upsize P0.02 via (40.75,43.5) while routing P0.02 if still open | — | Clear 2nd drill/via_diameter |
| 7 | P0.11 short stub 4.62 mm if clearance OK | (48.62,28.00)→(44.00,28.00) | May only merge fanout island; still need header |
| 8 | SIM_CLK / RST / IO / 1V8 private exits | South/east of U1, no RF box | −4 A |
| 9 | ADC group with new fanout vias + private B columns | P0.13/14/16–20; **keep P0.15 wrap** | Multiple A |
| 10 | Remaining J12/J13 GPIO + Class G duplicates | East headers x≈116 | Multiple A/G |
| 11 | MAGPIO/MIPI/COEX north-then-east | J14/J15 | −8 A |
| 12 | VDD_GPIO island merge + dangling via B stubs | Clears many of 82 dangling | A + dangling |
| 13 | Class C RF DNP stubs with RF Engineer | C22/C23/C24 only | −3 C |
| 14 | Zone refill → Class E GND | — | −9 E |
| 15 | After-DRC JSON | record **after** counts; ping Hardware PM with before/after | Gate check |

**Stop / escalate if:** any step raises `shorting_items` or `unconnected_items`, or requires entering RF keepout / matching copper.

---

## 6. Process gates (Hardware PM)

- Coordinate **RF keepouts** and Class C / matching with **RF Power Engineer via Hardware PM**.
- **No Gerbers** until `unconnected_items = 0` **and** DFM (`docs/FAB_READY_CHECKLIST.md`) signs off. Do not ask DFM for Gerbers while unconnected > 0.
- When a routing pass drops unconnected, capture **exact before/after** counts (and via_dangling / drill/via_diameter) for the PM ping.
- Stale `fab/gerbers/` (2026-09-16) must be replaced only after freeze — not used for fab now.

---

## 7. Session outcome — `layout-pass30-connect` (2026-09-23 09:51 IST)

| Item | Result |
| --- | --- |
| PCB copper edited | **Yes** (pcbnew 9.0.2 + `kicad-cli`) |
| Backup | `.mcp-backups/nRF9161-DEV-BOARD.kicad_pcb.pre-pass30-connect-20260923-094344` (+ `.mcp-backups/pass30-connect/start.kicad_pcb`) |
| **Before → after unconnected** | **79 → 80** (`reports/DRC_PASS30_BEFORE.json` / `DRC_PASS30_AFTER.json`) |
| Shorting before → after | **0 → 0** |
| Clearance before → after | **6 → 0** (zone refill; no new shorts) |
| via_dangling | **80 → 80** |
| drill_out_of_range / via_diameter | **0 → 0** (already fixed pre-pass) |
| Gerbers | **Not generated** |

### Placed / closed

| Item | Detail |
| --- | --- |
| **U3** | `TPS22919DCKR` footprint `SOT-363_SC-70-6` @ **(26.5, 47.0)** mm, orient 180° (east of RF keepout) |
| **FB5** | `L_0603_1608Metric` → **`L_0402_1005Metric`** @ **(23.8, 47.65)** orient 180° |
| Nets closed | **`GNSS_VBIAS_SRC`** U3.VOUT→FB5.1; **`GNSS_VBIAS`** FB5.2→bias-T (B.Cu); U3.GND stub |
| Class C | Stub attempts on C21–C24/C31–C32 where clearance allowed (DNP policy; trunks not ripped) |
| P0.15 west wrap | **Preserved** |

### Deferred (honest)

- **U3.VIN (`VDD_GPIO`)** and **U3.ON (`COEX0`)** — courtyard congestion (P0.00/P0.04/P0.13 walls + via forest). Ratsnest remains.
- Class F surgical (`VIN_FILT`, `VIN_F`, `SWDCLK`, `nRESET`, `P0.02`, `P0.08`) — blocked geometry; not forced.
- SIM / ADC / MAGPIO / MIPI / COEX header routes — stopped before risky RF edits.
- Schematic `04_GNSS`: U3 VIN/VOUT/GND global labels do not appear in netlist (ON=`COEX0` does); PCB nets assigned manually to match approved topology.

### Scripts / reports

- `scripts/final_pass30.py`, `scripts/final_pass30b.py`
- `reports/PASS30_SUMMARY.json`, `reports/DRC_PASS30_BEFORE.json`, `reports/DRC_PASS30_AFTER.json`
- Also `/tmp/drc_pass30_before.json`, `/tmp/drc_pass30_after.json`

**Success gate:** clear progress (U3 placed + FB5 0402 + bias path closed) with shorts held at 0; unconnected +1 from new U3 EN/VIN pads still open.

---

## 8. RF layout locks (still in force)

1. West RF keepout x≈**0–24.2**, y≈**20–64** — respected (U3 placed at x=26.5).
2. Class C DNP stub-terminate policy — applied where clear.
3. Do not split In1 GND under 50 Ω; no digital under matching on F.Cu.

---

*End of PCB Layout Review — pass30-connect 2026-09-23 IST*

---

## Pass30c (2026-09-23 10:03 IST)

**Goal:** Sync schematic U3 nets, then close U3.VIN / U3.ON and Class F surgically.

| Metric | Before | After |
| --- | ---: | ---: |
| unconnected_items | **80** | **78** |
| shorting_items | 0 | 0 |
| clearance | 0 | 0 |
| hole_clearance | 0 | 0 |

**Netlist sync:** `reports/netlist_after_u3.xml` + ERC Errors=0 (`reports/ERC_U3_after.rpt`). U3 signal pads already matched schematic (`VDD_GPIO` / `GND` / `COEX0` / `GNSS_VBIAS_SRC`); pads 4/5 assigned `unconnected-(U3-NC-Pad4)` / `unconnected-(U3-QOD-Pad5)`. No manual VIN/VOUT/ON overrides retained beyond netlist.

**Closed:**
- `VDD_GPIO` U3.1 VIN — F stub to via (28.5, 40) then B north to (40.17, 19.13)
- `COEX0` U3.3 ON — F west-north-east around VIN (26.2 → 38 corridor) to via (33, 43) then B to spine (38.8, 43)

**Still open (priority leftovers):**
- Class F: `VIN_FILT`, `VIN_F`, `SWDCLK`, `nRESET`, `P0.02`, `P0.08` (power/debug congestion; no safe path without clearance hits)
- `COEX0` north island still split from south F stub (`F@38.75,37.25` ↔ `via@31.11,22`)
- Other `VDD_GPIO` header/island opens (U3 pad itself is connected)
- SIM / ADC / MAGPIO / MIPI / COEX headers

**Constraints held:** shorting=0; clearance=0; P0.15 B.Cu west wrap intact (17 segments); no Gerbers; RF keepout x≈0–24.2 respected for new copper (U3 routes x≥26.2).

**Backup:** `.mcp-backups/nRF9161-DEV-BOARD.kicad_pcb.pre-pass30c-20260923-095159`  
**DRC:** `reports/DRC_PASS30C_BEFORE.json`, `reports/DRC_PASS30C_AFTER.json`  
**Summary:** `reports/PASS30C_SUMMARY.json`

---

## Pass30d (2026-09-23 IST)

**Goal:** Drop unconnected below 78 by closing Class F (`VIN_FILT`→`VIN_F`→`SWDCLK`→`nRESET`→`P0.02`/`P0.08`) plus easy `COEX0` north island. Aggressive non-critical blocker jogs allowed; keep shorting=0; do not rip P0.15 west wrap; RF keepout intact.

| Metric | Before | After |
| --- | ---: | ---: |
| unconnected_items | **78** | **78** |
| shorting_items | 0 | 0 |
| clearance | 0 | 0 |

**Closed:** none (all Class F attempts aborted or failed clearance).

**What blocked (honest):**
- `VIN_FILT`: geometric B corridor from via(55.35,13.3) to via(51.9,21.9) requires gap through `VDD_GPIO` H@y=14.8 + `P0.15` north trunk@y=15.35 + `ENABLE` H@y=20.3 + `VDD2` H/V. Simulated deep/north reconnect jogs made the path clear in `track_clear`, but live DRC reported **shorting_items=10 / tracks_crossing=11** — copper discarded.
- `P0.08`: farthest progress — jogged `COEX2` V@x=72, `ENABLE` V@x=62.5, `ENABLE` H@y=28; then blocked by `VDD1` via@53.7 and `P0.10`/`P0.11` via forest near dest via@46.2.
- `VIN_F` / `SWDCLK` / `nRESET` / `P0.02` / `COEX0`: via/track forests; no safe DRC-clean path found.

**Constraints held:** shorting=0 (failed attempts restored); P0.15 west wrap intact; RF keepout respected; no Gerbers.

**Backup:** `.mcp-backups/nRF9161-DEV-BOARD.kicad_pcb.pre-pass30d-20260923-100505`  
**DRC:** `reports/DRC_PASS30D_BEFORE.json`, `reports/DRC_PASS30D_AFTER.json`  
**Summary:** `reports/PASS30D_SUMMARY.json`

---

## Pass30e (2026-09-23 16:04 IST)

**Goal:** Co-route VIN_FILT with ENABLE fully restored; P0.08 if corridors allow.

| Metric | Before | After |
| --- | ---: | ---: |
| unconnected_items | **78** | **78** |
| shorting_items | 0 | 0 |
| clearance | 0 | 0 |

**Closed:** none. VDD_GPIO + P0.15 restores proven in isolation; **ENABLE@y20.3 restore failed** (VDD1 / C5–C6 / VIN_FILT F spine). All trial copper reverted.

**Backup:** `.mcp-backups/nRF9161-DEV-BOARD.kicad_pcb.pre-pass30e-20260923-102320`  
**DRC:** `reports/DRC_PASS30E_BEFORE.json`, `reports/DRC_PASS30E_AFTER.json`  
**Summary:** `reports/PASS30E_SUMMARY.json`

---

## Pass30f (2026-09-23 10:42 IST)

**Goal:** ONE atomic co-route — close VIN_FILT (and VIN_F if cheap) with ENABLE fully restored in the same transaction; P0.08 if corridors allow. Drive unconnected below 78; shorting=0 clearance=0. No footprint moves. No Gerbers.

| Metric | Before | After |
| --- | ---: | ---: |
| unconnected_items | **78** | **78** |
| shorting_items | 0 | 0 |
| clearance | 0 | 0 |
| tracks_crossing | 0 | 0 |

**Closed:** `VIN_FILT` (B.Cu path (55.35,13.3)→(51.9,13.3)→(51.9,21.9) w=0.30). Count stayed 78 because Class-E F.Cu GND zone-island reports went 9→10 (fill artifact @ ≈−0.05,−0.05).

**Ripped + restored (kept on board):**
- `VDD_GPIO` H@y14.8 → north U @y=9.0
- `P0.15` north trunk@y15.35 (west wrap untouched, 21 segs) → F via-bridge vias@(51.0,16.5)/(60.0,16.5) + F@y19.5
- `ENABLE` H@y20.3 → F via-bridge via existing (50.85,23.15)/(56.50,20.30)
- `VDD2_MID` H@y16.87 → south U @y17.8 (needed so P0.15 east via does not short)

**P0.08:** probe after ripping ENABLE H@y28 + V@x62.5 + COEX2@x72 — still blocked (VDD_nRF via@69.3,30 and via/pad forest). Probe only; live board not polluted.

**VIN_F / SWDCLK:** deferred to 30g (not cheap after this cycle).

**STOP:** unconnected still 78 → no further thrash. Placement-move proposals (≤3 mm, do **not** move without Hardware PM):
| Ref | Current xy | Proposed Δ | Why |
| --- | --- | --- | --- |
| TP11 | (60.0, 30.0) | +y 2.5 → (60.0, 32.5) | Free F y≈30 for P0.08 |
| R2 | (58.0, 26.0) | −y 2.0 → (58.0, 24.0) | Clear F y≈28 ENABLE/P0.08 |
| C6 | (51.0, 27.0) | −x 2.0 → (49.0, 27.0) | Open B column near ENABLE/VDD1 |
| TP19 | (52.0, 22.0) | +x 2.5 → (54.5, 22.0) | Off VIN_FILT/ENABLE F spine |

**Constraints held:** shorting=0; clearance=0; P0.15 west wrap intact; RF keepout / matching / U3 GNSS bias untouched; no footprint moves; no Gerbers.

**Backup:** `.mcp-backups/nRF9161-DEV-BOARD.kicad_pcb.pre-pass30f-20260923-103606`  
**DRC:** `reports/DRC_PASS30F_BEFORE.json`, `reports/DRC_PASS30F_AFTER.json`  
**Summary:** `reports/PASS30F_SUMMARY.json`

---

## Pass30g (2026-09-23 IST)

**Goal:** ONE honest cycle — apply Hardware-PM-approved four placement moves, zone refill, close P0.08 (then VIN_F/SWDCLK if cheap). shorting=0 clearance=0. No Gerbers. Protect P0.15 west wrap + RF/U3.

| Metric | Before | After (restored) |
| --- | ---: | ---: |
| unconnected_items | **78** | **78** |
| shorting_items | 0 | 0 |
| clearance | 0 | 0 |

**Result: STOP — placement set not DRC-legal; board reverted.**

### What was attempted
| Ref | Requested | Outcome |
| --- | --- | --- |
| TP11 | (60,30)→(60,32.5) | Applied in bundle; **reverted** (bundle shorting) |
| R2 | (58,26)→(58,24) | **SKIPPED** — R2.1 VIN_FILT @(58,22.54) overlaps TP20 VDD_nRF @(58,22) |
| C6 | (51,27)→(49,27) | Applied; VDD1 reattach along x≈48.7 shorts **DEC0/P0.11**; **reverted** |
| TP19 | (52,22)→(54.5,22) | Applied; pad shorts **VDD2 via@(54.50,21.20)**; **reverted** |
| VDD_nRF via | (69.3,30)→(69.3,28) | Attempted with bundle; **reverted** |

Mid-attempt DRC (not kept): shorting=11, tracks_crossing=7.

### P0.08
Not closable this cycle. Even prior /tmp probes with TP11/C6/TP19 + via jog + ENABLE/COEX2 rip remain walled by **VDD2 verticals** @x=52.22 and @x=54.50 on B@y≈30.

### Next proposals (need Hardware PM)
1. **TP20** (58,22)→(56,20) — unlock R2→(58,24)
2. **Revise TP19** target — (54.5,22) illegal; try (56.5,22) or (52,20)
3. **VDD2 via-bridge / east U-jog** at y≈30 (primary B corridor wall)
4. **C6 VDD1 reattach** via existing via@(49.2,25.6) — avoid DEC0 column
5. Optional **GND via** (80,30)→(80,32.5) for dest approach

**Constraints held on live board:** shorting=0; clearance=0; P0.15 west wrap 21 segs; RF keepout / U3 untouched; no Gerbers; no footprint moves left on board.

**Backup:** `.mcp-backups/nRF9161-DEV-BOARD.kicad_pcb.pre-pass30g-20260923-104551`  
**DRC:** `reports/DRC_PASS30G_BEFORE.json`, `reports/DRC_PASS30G_MID.json`, `reports/DRC_PASS30G_AFTER.json`  
**Summary:** `reports/PASS30G_SUMMARY.json`

---

## Pass30h (2026-09-23 11:07 IST)

**Goal:** ONE honest cycle — Stage A copper-only first (VDD2 via-bridge, optional GND via, VDD_nRF via jog); Stage B placement only if still needed; zone refill; close P0.08 (ENABLE H@y28 rip/restore OK); VIN_F/SWDCLK if cheap. shorting=0 clearance=0. No Gerbers. Protect P0.15 west wrap + RF/U3.

| Metric | Before | After |
| --- | ---: | ---: |
| unconnected_items | **78** | **78** |
| shorting_items | 0 | 0 |
| clearance | 0 | 0 |
| tracks_crossing | 0 | 0 |

**Result: STOP — Stage A kept; P0.08 and Stage B reverted; no signal-net drop.**

### Stage A (applied, DRC clean)
| Edit | Detail | Result |
| --- | --- | --- |
| VDD2 B walls | Rip (52.22,26.75)–(52.22,32) and (54.5,21.2)–(54.5,32) | Done |
| VDD2 via-bridge | Vias@(58,29.55)/(58,30.95) + F hop; south B feeder @y=29.55; north via stitches to y=32 (no north feeder across corridor) | Done |
| VDD_nRF via | (69.3,30)→(**69.3,31.5**) north ≤2 mm — not south onto VIN_FILT F@y28.8 | Done |
| GND via | (80,30)→(80,32.5) | **SKIPPED** — shorts VDD_GPIO F |

### P0.08
Probe after Stage A + ENABLE/COEX2 temp rip: **CLEAR** `B_y30.25` path `(46.2,30)→(46.2,30.25)→(78.5,30.25)→(78.5,26)→(79.67,26)`.  
Live commit with original ENABLE/COEX2 restore → `tracks_crossing=4` (ENABLE x=62.5/76.8, H@y28, COEX2 x=72). Jogged restore → clearance vs VDD_GPIO via. **P0.08 copper REVERTED.**

### Stage B (reverted)
TP20→(56,20), R2→(58,24), TP11→(60,32.5), TP19→(52,20), C6→(49,27). Mid DRC shorting=5 clearance=2 crossing=7. **Root:** C6@(49,27) places pad1 at **x=48.68** (forbidden DEC0/P0.11 column). Bundle reverted; Stage A preserved.

### Signal deltas
None (empty). Class-E GND islands unchanged (total still 78).

### Next proposals
1. **Atomic ENABLE/COEX2 + P0.08 co-route** — rip crossing segments, place P0.08 @y30.25, restore ENABLE/COEX2 with jogs pre-cleared vs VDD_GPIO vias
2. **C6 reattach** — after C6→(49,27), stitch **only** via@(49.2,25.6) with path x≥49.0 (never x≈48.7 vertical)
3. Optional GND via jog needs a clearance-safe target (not 80,32.5)

**Constraints held:** shorting=0; clearance=0; tracks_crossing=0; P0.15 west wrap preserved; RF keepout / U3 untouched; no Gerbers.

**Backup:** `.mcp-backups/nRF9161-DEV-BOARD.kicad_pcb.pre-pass30h-20260923-105755`  
**DRC:** `reports/DRC_PASS30H_BEFORE.json`, `reports/DRC_PASS30H_MID.json`, `reports/DRC_PASS30H_AFTER.json`  
**Summary:** `reports/PASS30H_SUMMARY.json`

---

## Pass30i — atomic P0.08 co-route (2026-09-23 11:12 IST)

**Goal:** Atomic ENABLE/COEX2 + P0.08 co-route on Stage A board. No placement. shorting=0 clearance=0.

**Result: KEEP — unconnected 78→77; P0.08 U1↔SW3/R14 closed.**

### Geometry kept
- **P0.08** B: `(46.2,30)→(46.2,30.25)→(78.5,30.25)→(78.5,26)→(79.67,26)` w=0.18
- **ENABLE @x=62.5** via-bridge: vias@(62.5,29.6)/(62.5,30.9) + F hop (B U-jog impossible across P0.08 H)
- **COEX2 @x=72** via-bridge: vias@(72,30.9)/(72,29.6) + F hop
- **ENABLE east**: via-bridge vias@(76.8,30.9)/(79.2,30.9) + F hop; B reconnect `(79.2,28)→(90.38,28)`

### Remaining
- **P0.08 → J12.9** — closed in pass30j
- Class E GND islands / other Class F (VIN_F, SWDCLK, nRESET) unchanged
- Stage B placement still illegal (C6.1 DEC0) — not attempted

### Next proposals
1. Route P0.08 west/south stub to J12.9 (private column; protect P0.15 wrap)
2. VIN_F / SWDCLK Class F if corridor free after P0.08 east copper
3. Stage B C6 reattach only with pad1 stitch x≥49.0 (never vertical @x=48.68)

---

## Pass30j — P0.08 → J12.9 stitch (2026-09-23 11:24 IST)

**Goal:** Stitch P0.08 from pass30i island (U1↔SW3/R14) to J12.9. Keep Stage A + pass30i ENABLE/COEX2/P0.08 trunk. No placement. shorting=0 clearance=0.

**Result: KEEP — unconnected 77→76; P0.08 fully closed to J12.9.**

### Geometry kept
- **P0.08 trunk** (pass30i) untouched: B `(46.2,30)→…→(79.67,26)`
- **Branch** B@x=65.2 from H@y30.25 south with F via-hops:
  - COEX2 @y38 → vias 37.45/38.55
  - COEX0 @y62 → vias 61.45/62.55
  - P0.18+P0.17 @y72.8/73.4 → vias 72.25/73.95
- **Bottom** B H@y79 `(65.2,79)→(26.32,79)` → B drop → via(26.32,78) → F to J12.9 pad
- **Restores (same transaction):**
  - P0.15 bottom H: wide F-bridge vias@(61.5,77.45)/(68.5,77.45)
  - P0.01: final F-bridge 24.5–27.2 @y78.5 + column U-jog F@y74.5 (62–68)

### Trial note
First restore pair (P0.15@77.45 + P0.01 U-jog@77.8) caused shorting=5/clearance=3 — **reverted**; widened/separated restores then KEPT.

### Remaining / deferred
- VIN_F / SWDCLK: skipped this cycle (Class F still congested; not cheap)
- Class E GND islands / other Class F unchanged
- No Gerbers

**Backup:** `.mcp-backups/nRF9161-DEV-BOARD.kicad_pcb.pre-pass30j-20260923-112326`  
**DRC:** `reports/DRC_PASS30J_BEFORE.json`, `reports/DRC_PASS30J_MID.json`, `reports/DRC_PASS30J_AFTER.json`  
**Summary:** `reports/PASS30J_SUMMARY.json`

---

## Pass30k — Class F VIN_F close (2026-09-23 11:34 IST)

**Goal:** Class F order VIN_F → SWDCLK → nRESET → P0.02 (one net at a time; DRC-clean before next). Keep Stage A + pass30i/30j. Co-restore ripped nets. shorting=0 clearance=0. No placement. No Gerbers. Stop after two Class-F restore failures.

**Result: KEEP — unconnected 76→75; VIN_F closed.**

### Geometry kept
- **VIN_F** B: `(49.30,12.60)→(49.30,11.00)→(69.20,11.00)` w=0.30
- **VIN_F** F-hop over VDD_GPIO V@x70: vias@(69.20,11.00)/(70.80,11.00) + F H
- **VIN_F** B: `(70.80,11.00)→(70.80,16.20)→(71.575,16.20)→(71.575,19.062)` into FB4 island
- **P0.15 restore:** east H@y15.35 F-bridge vias@(69.30,15.35)/(72.00,15.35); B keep 60→69.3
- **VDD_GPIO** intact (no rip — hopped on F)

### Blocked / deferred (one honest cycle each)
- **SWDCLK:** B west column after VDD_GPIO H@19.13 rip is geometrically clear, but V@x48.05 restore hits J8.3 GND @(48.05,4.73). No live copper left.
- **nRESET:** H corridors congested (VIN_FILT / VDD2 / P0.15 / VIN_F / ENABLE vias). Left untouched.
- **P0.02 / COEX0:** not attempted — STOP after two Class-F restore failures.

### Preserved
- Stage A VDD2 via-bridge + VDD_nRF via north
- pass30i ENABLE/COEX2 + P0.08 trunk H@y30.25 + pass30j J12.9 stitch
- P0.15 west wrap (21 segs)
- RF keepout / U3/GNSS bias

**Backup:** `.mcp-backups/nRF9161-DEV-BOARD.kicad_pcb.pre-pass30k-20260923-112757`  
**DRC:** `reports/DRC_PASS30K_BEFORE.json`, `reports/DRC_PASS30K_MID_VINF.json`, `reports/DRC_PASS30K_AFTER.json`  
**Summary:** `reports/PASS30K_SUMMARY.json`

---

## Pass30l — SWDCLK F/mixed detour around J8.3 (2026-09-23 11:40 IST)

**Goal:** Class F order SWDCLK → nRESET → P0.02; if Class F stalls, option C cheap signal islands. Keep Stage A + pass30i–30k. F.Cu/mixed detour around J8.3 GND without moving J8. Co-restore VDD_GPIO if ripped. shorting=0 clearance=0. No Gerbers.

**Result: KEEP — unconnected 75→74; SWDCLK U1.33↔J8.4 closed.**

### Geometry kept (SWDCLK)
- F stub `(37.75,26.75)→(37.75,24.8)` + via
- B west column `@x=34.2`: `(37.75,24.8)→(34.2,24.8)→(34.2,19.8)`
- F-hop over intact VDD_GPIO H@y19.13: vias@(34.2,19.8)/(34.2,18.4)
- B `(34.2,18.4)→(34.2,1.5)` + via
- F north band around J8.3: `(34.2,1.5)→(53.65,1.5)→(53.65,4.73)` into existing SWDCLK via
- **No VDD_GPIO rip. No J8 move.**

### Blocked / deferred
- **nRESET:** one probe B@y12.6 with F-hops @ENABLE/VIN_F → shorting=1 clearance=1 crossing=3 — **reverted atomically**
- **P0.02:** not attempted (nRESET not closed; avoid thrash)
- **Option C:** candidates MAGPIO1/MIPI_VIO/AUX_FIT/P0.16/… scanned; AUX_FIT @x19.52 hits RF (GPS/ANT_FIT/GNSS_VBIAS); COEX0 touches U3 — skipped

### Preserved
- Stage A VDD2 via-bridge + VDD_nRF via north @(69.3,31.5)
- pass30i–30k ENABLE/COEX2/P0.08/VIN_F/P0.15 restores
- P0.15 west wrap (21 segs)
- RF keepout / U3

### Signal deltas
| Net | Δ unconnected |
| --- | --- |
| SWDCLK | −1 |
| nRESET | 0 |
| P0.02 | 0 |
| others watched | 0 |

### J8 proposal (NOT applied — needs new OK)
None required this cycle (SWDCLK closed without placement). If future B@x48.05 restore still desired: J8 `(50.0,6.0)→(50.0,3.5)` Δ=2.5 mm north — opens pad clearance vs VDD_GPIO V@x48.05 (only if a later pass re-needs that column).

**Backup:** `.mcp-backups/nRF9161-DEV-BOARD.kicad_pcb.pre-pass30l-20260923-114002`  
**DRC:** `reports/DRC_PASS30L_BEFORE.json`, `reports/DRC_PASS30L_MID.json`, `reports/DRC_PASS30L_MID_NRESET.json`, `reports/DRC_PASS30L_AFTER.json`  
**Summary:** `reports/PASS30L_SUMMARY.json`

---

## Pass30m — deeper nRESET co-route (2026-09-23 11:44 IST)

### Goal
Atomic nRESET B@y12.6 co-route with preflight-recorded rip list. Restore ripped nets in same transaction. shorting=0 clearance=0. No Gerbers.

### Preflight rip list (recorded before copper edit)
- `P015_EAST_B_V_72`: P0.15 B.Cu (72.0,15.35)→(72.0,7.2) w=0.18 — B vertical crosses corridor @y=12.6
- ENABLE / VIN_FILT H / VDD2: **not ripped** (no overlap at y=12.6)
- VIN_F / P0.08 / SWDCLK: **not ripped** (hard ban)

### Attempt
- Rip P0.15 east stub → nRESET B@y12.6 with F-hop (69.0–71.5) → restore P0.15 F-bridge vias@(72,13.8)/(72,11.4)

### Result
- **nRESET closed:** no
- **Reverted:** yes (full transaction from `pre-nreset-tx.kicad_pcb`)
- **Before unconnected:** 74
- **Mid unconnected:** 73 (shorting=0 clearance=1 crossing=2)
- **After unconnected:** 74
- **P0.15 west segs:** preserved (21)
- **P0.02:** not attempted

### Colliding copper (mid DRC — reason for revert)
- tracks_crossing: nRESET B@y12.6 × COEX2 B
- tracks_crossing: nRESET B@y12.6 × P0.01 B
- clearance: nRESET B vs VDD_nRF via@(57.95, 12.0) (actual 0.11 < 0.15 POWER)

### Artifacts
- Backup: `.mcp-backups/nRF9161-DEV-BOARD.kicad_pcb.pre-pass30m-20260923-114330`
- DRC: `reports/DRC_PASS30M_BEFORE.json`, `reports/DRC_PASS30M_MID.json`, `reports/DRC_PASS30M_AFTER.json`
- Summary: `reports/PASS30M_SUMMARY.json`

---

## Pass30n — nRESET co-route + COEX2/P0.01 rip-restore (2026-09-23 11:52 IST)

### Goal
Atomic nRESET with ≥0.15 mm clearance to VDD_nRF via@(57.95,12) d=0.8. Rip P0.15 east + COEX2 + P0.01 crossed segs; co-restore before DRC. shorting=0 clearance=0 crossing=0. No Gerbers.

### Preflight rip list (recorded before copper edit)
- `P015_EAST_B_V_72`: P0.15 B.Cu (72.0,15.35)→(72.0,7.2) w=0.18 — B vertical crosses nRESET corridor @y=12.6; local east stub rip allowed (as pass30m)
- `COEX2_B_H_246`: COEX2 B.Cu (72.0,24.6)→(105.1,24.6) w=0.18 — B H crossed by nRESET east attach V@x=101.68 y=12.6→26.0 (pass30m mid crossing)
- `P001_B_H_152`: P0.01 B.Cu (86.14,15.2)→(105.55,15.2) w=0.18 — B H crossed by nRESET east attach V@x=101.68 y=12.6→26.0 (pass30m mid crossing)

### Attempt
- Clearance: F@y=10.8 from x=53.65→59.4 under JP1/VDD_nRF (no via near JP1 pads; expect clr ~0.71 mm to via d=0.8)
- F-hop 69.0–71.5 over VDD_GPIO/VIN_F (no rip)
- Co-restore: COEX2 F-hop @y22.5 south of SW2; P0.01 F-hop @y15.2; P0.15 east F-bridge

### Result
- **nRESET closed/KEPT:** yes
- **Reverted:** no
- **Before unconnected:** 74
- **Mid/After unconnected:** 73 (shorting=0 clearance=0 crossing=0)
- **P0.15 west segs:** {'before': 21, 'after': 21, 'preserved': True}
- **P0.02:** Skipped — no free corridor identified without additional rips this cycle (only after nRESET KEPT; defer)
- **Backup:** `.mcp-backups/nRF9161-DEV-BOARD.kicad_pcb.pre-pass30n-20260923-115144`
- **DRC:** `reports/DRC_PASS30N_BEFORE.json`, `reports/DRC_PASS30N_MID.json`, `reports/DRC_PASS30N_AFTER.json`
- **Summary:** `reports/PASS30N_SUMMARY.json`

### Signal deltas
| Net | Δ unconnected |
| --- | --- |
| nRESET | -1 |
| P0.02 | 0 |
| COEX2 | 0 |
| P0.01 | 0 |
| P0.15 | 0 |

---

## Pass30o — P0.02 close (2026-09-23 12:03 IST)

### Goal
P0.02 first with atomic rip/restore of non-banned blockers; then cheap true signal islands/header stubs. shorting=0 clearance=0 crossing=0. No Gerbers. Protect Stage A + pass30i–30n kept copper + P0.15 west wrap + RF/U3.

### Preflight rip list
- `VDD_GPIO_B_V_4805`: VDD_GPIO B.Cu (48.05,3.46)→(48.05,14.80) — crosses P0.02 H@y4.5; U-jog west restore
- `P001_B_H_152`: P0.01 B.Cu (86.14,15.2)→(100.3,15.2) — crossed by P0.02 east col @x89
- `P015_EAST_B_H_72`: P0.15 B.Cu (72.0,7.2)→(106.0,7.2) — east H only (not west wrap)

### Geometry kept (P0.02)
- West: from existing B@y45.8 via col **x=27.5** with F-hops over P0.06@44.5 / P0.13@43–41
- Corridor: B **H@y=4.5** with F-hops over SWDCLK@x34.2 + VDD_GPIO U@x45; **north jog** around SWDCLK via@(53.65,4.73)
- East: col **x=89** F-hop over nRESET@y12.6 → attach (89,19.13)→(92.14,19.13) into existing via
- Restores: VDD_GPIO U-jog west; P0.01/P0.15 F-hops 88.2–89.8

### Result
- **Closed/KEPT:** P0.02
- **Reverted:** no
- **Before unconnected:** 73
- **After unconnected:** 72 (shorting=0 clearance=0 crossing=0)
- **P0.15 west segs:** before=21 after=21 preserved=True
- **Stage A:** {'VDD_nRF_via_north': True, 'VDD2_vias': 2, 'VDD2_present': True}
- **Cheap islands:** scanned ['MAGPIO0', 'MAGPIO1', 'MAGPIO2', 'MIPI_SCLK', 'MIPI_SDATA', 'MIPI_VIO', 'P0.00', 'P0.01', 'P0.03', 'P0.14', 'P0.16', 'P0.20'] — none committed (no pre-cleared stub this cycle)
- **Backup:** `.mcp-backups/nRF9161-DEV-BOARD.kicad_pcb.pre-pass30o-20260923-120037`
- **DRC:** `reports/DRC_PASS30O_BEFORE.json`, `reports/DRC_PASS30O_MID.json`, `reports/DRC_PASS30O_AFTER.json`
- **Summary:** `reports/PASS30O_SUMMARY.json`

### Signal deltas
| Net | Δ unconnected |
| --- | --- |
| P0.02 | -1 |
| VDD_GPIO | 0 |
| P0.01 | 0 |
| P0.15 | 0 |
| nRESET | 0 |

---

## Pass30p — P0.22 → P0.11 → pairs/MAGPIO/AUX (2026-09-23 12:13 IST)

### Goal
Lock order P0.22 → P0.11 → P0.10/17/31 pairs + MAGPIO/MIPI/AUX true opens. Skip Class-E GND zone islands. VDD_GPIO last/careful (deferred). shorting=0 clearance=0 crossing=0. No Gerbers. Protect Stage A + pass30i–30o + P0.15 west wrap + RF/U3. Two restore fails → STOP.

### Result
- **Closed/KEPT:** ['P0.22 (U1↔J8 island)', 'P0.11 (U1 fanout into existing B island)']
- **Reverted attempts:** 3 (all atomic; restore_fail_streak=0)
- **Before unconnected:** 72
- **After unconnected:** 70 (shorting=0 clearance=0 crossing=0)
- **P0.15 west segs:** {'before': 21, 'after': 21, 'preserved': True}
- **Stage A:** {'VDD_nRF_via_north': True, 'VDD2_vias': 2, 'VDD2_present': True}

### Geometry kept
- **P0.22 U1↔J8:** F fanout (35.25,26.75)→via(35.25,22); F-hop VDD_GPIO H@y19.13; B north-band y=2 with F-hops over P0.02 @x36.5 and @x64; attach into existing via(53.65,6) / J8.6 stub
- **P0.11 U1 fanout:** F (44,28)→(46.5,28) + via + B (46.5,28)→(46.5,29.2) into existing B island

### Blocked / deferred
- **P0.22_J13_J10:** South/east header pair blocked by P0.01/P0.15/VDD_GPIO dual-layer corridors; deferred
- **P0.11_J12_J16:** Header extensions congested (P0.15/P0.16/VDD_GPIO/VIN_F); U1-only keep this cycle
- **P0.10:** Same class as P0.11; fanout exists; header runs not pre-cleared
- **P0.17:** U1 via island ↔ bottom J13/J18 island: x42 south hits P0.13/COEX2/P0.04; y50 H clear but COEX0@58.8 on x48.16
- **P0.31:** PAD-ONLY (U1.89, J13.16, J11.2) — no copper; see placement_proposal
- **MAGPIO0_2_MIPI:** Long U1→J14 runs; fanouts only; no pre-cleared stub
- **AUX:** Two DRC-failed probes (RF_50OHM clr to GPS/GNSS_ANT; GNSS_VBIAS B short) — reverted atomically
- **AUX_FIT:** RF keepout path (skipped)
- **VDD_GPIO:** Deferred (power last; no thrash this cycle)

### Placement proposal (NOT applied — needs new OK)
- Net **P0.31**: Three pads, zero copper; no DRC-clean corridor found without cutting protected copper
- {'move': 'J11', 'from': [116.0, 48.54], 'to': [116.0, 45.54], 'delta_mm': 3.0, 'note': 'Nudge J11 3mm north may open east-edge column vs VDD_GPIO@38.8/51 — NOT applied'}
- {'move': 'J13', 'from': [102.1, 76.0], 'to': [102.1, 73.0], 'delta_mm': 3.0, 'note': 'Nudge J13 3mm north toward interior corridors — NOT applied'}
- {'move': 'U1', 'note': 'Do not move SoC; prefer header nudge ≤3mm if future OK'}

### Signal net deltas (excl. GND zone noise)
| Net | Δ unconnected |
| --- | --- |
| P0.11 | -1 |
| P0.22 | -1 |

### GND zone deltas
| Net | Δ |
| --- | --- |
| (none — Class-E skipped) | 0 |

**Backup:** `.mcp-backups/nRF9161-DEV-BOARD.kicad_pcb.pre-pass30p-20260923-120436`  
**DRC:** `reports/DRC_PASS30P_BEFORE.json`, `reports/DRC_PASS30P_MID_P022.json`, `reports/DRC_PASS30P_MID_P011.json`, `reports/DRC_PASS30P_AFTER.json`  
**Summary:** `reports/PASS30P_SUMMARY.json`

---

## Pass30q — P0.22 J13↔J10 then stubs (2026-09-23 12:22 IST)

### Goal
Copper-first: close remaining P0.22 J13↔J10 island, then P0.11 header stubs, then P0.10/P0.17 if corridor opens. Skip GND zone noise. VDD_GPIO last/careful (deferred). shorting=0 clearance=0 crossing=0. No Gerbers. Protect Stage A + pass30i–30p + P0.15 west wrap + RF/U3. Two restore fails → STOP.

**PM OK (conditional):** J13 only `(102.1, 76.0)→(102.1, 73.0)` if P0.31 still pad-blocked after copper attempts. J11 **not** approved. Never move U1. After J13 move: reattach all J13 nets + stitch P0.31 same cycle if clean.

### Result
- **Closed/KEPT:** none
- **Reverted attempts:** 2 (both P0.22; atomic restore OK; **restore_fail_streak=2 → STOP**)
- **Before unconnected:** 70
- **After unconnected:** 70 (shorting=0 clearance=0 crossing=0)
- **P0.15 west segs:** before=21 after=21 preserved=True
- **Stage A:** VDD_nRF via north @ (69.3,31.5) + VDD2 via-bridge present
- **J13 move:** **not applied** (STOP before P0.31 copper attempts; copper-first gate)

### Attempts (P0.22 J13.7↔J10.2)
- Corridor found: B stub@x79.24 → F-hop P0.01@80.51 → B H@y71.5 → F-hop wall (P0.01@105.55+P0.15@106) → B col@x109.2 with F-hop over P0.06@y55.5 → east jog.
- **Attempt1 REVERT:** attach via@(112.5,30.54) clearance **0.115&lt;0.15** vs VDD_GPIO F H@y31.08 (POWER).
- **Attempt2 REVERT:** F-only attach (111.8,30.54)→J10.2 **tracks_crossing** VDD_GPIO F H@y31.08.
- **Next-path note (not applied):** B-side attach with F-hop vias at **y≤29.9** over P0.04@113.8 / P0.06@113.2, then B into J10.2 PTH — keeps clear of VDD_GPIO F@y31.08.

### Blocked / deferred
- **P0.22_J13_J10:** STOP after 2 restore fails (see next-path note)
- **P0.11 / P0.10 / P0.17:** Not attempted — STOP
- **P0.31:** Still PAD-ONLY (U1.89, J13.16, J11.2); J13 move approved but gated behind copper attempts (not reached)
- **VDD_GPIO:** Deferred; also the J10 attach blocker
- **GND:** Skipped (zone noise)

### Signal net deltas (excl. GND zone noise)
| Net | Δ unconnected |
| --- | --- |
| (none) | 0 |

### GND zone deltas
| Net | Δ |
| --- | --- |
| (none — Class-E skipped) | 0 |

**Backup:** `.mcp-backups/nRF9161-DEV-BOARD.kicad_pcb.pre-pass30q-20260923-121611`  
**DRC:** `reports/DRC_PASS30Q_BEFORE.json`, `reports/DRC_PASS30Q_MID_P022.json`, `reports/DRC_PASS30Q_MID_P022b.json`, `reports/DRC_PASS30Q_AFTER.json`  
**Summary:** `reports/PASS30Q_SUMMARY.json`

## Pass30r — P0.22 B-attach → headers → J13+P0.31 (2026-09-23 12:31 IST)

### Goal
One P0.22 B-attach geometry only; if new collision STOP. Then headers; then J13 move+P0.31.
Protect Stage A + pass30i–30q KEEP + P0.15 west wrap + RF/U3. No Gerbers. J11/U1 never move.

### Result
- **Phase:** COMPLETE_P022_ONLY
- **Closed/KEPT:** ['P0.22 J13.7↔J10.2 (B-attach y29.9)']
- **P0.22 kept:** True — unconnected 70→69, P0.22 2→1, shorting=clearance=crossing=0
- **Headers:** Deferred (congested P0.11/P0.10/P0.17 corridors)
- **J13 move+P0.31:** **REVERTED** — shorting=7 clearance=3 crossing=27 (J13 pad shorts into existing B copper @y≈72.8; P0.31 B@y39.5 crossed SIM_CLK/VDD2/ENABLE). Board restored to P0.22-keep.
- **J13 position:** unchanged at (64.0, 76.0)
- **P0.15 west segs:** 21→21 preserved
- **Stage A:** VDD_nRF via north + VDD2 via-bridge present
- **Blocked:** {
  "P0.11_J12_J16": "Deferred \u2014 congested (P0.15/P0.16/VDD_GPIO/VIN_F); no pre-cleared stub",
  "P0.10": "Deferred \u2014 same class as P0.11",
  "P0.17": "Deferred \u2014 U1\u2194J18 blocked (COEX0/P0.13)",
  "P0.31": "dirty={'unconnected_items': 69, 'shorting_items': 7, 'clearance': 3, 'tracks_crossing': 27, 'via_dangling': 71}; collide=[{'type': 'shorting_items', 'description': 'Items shorting two nets (nets P0.17 and P0.18)', 'items': [{'description': 'PTH pad 2 [P0.17] of J13', 'pos': {'x': 66.54, 'y': 73.0}}, {'description': 'Track [P0.18] on B.Cu, length 18.3800 mm', 'pos': {'x': 69.08, 'y': 72.8}}]}, {'type': 'shorting_items', 'description': 'Items shorting two nets (nets P0.17 and P0.18)', 'items': [{'description': 'PTH pad 2 [P0.17] of J13', 'pos': {'x': 66.54, 'y': 73.0}}, {'description': 'Track [P0.18] on B.Cu, length 18.3800 mm', 'pos': {'x': 69.08, 'y': 72.8}}]}, {'type': 'tracks_crossing', 'description': 'Tracks crossing', 'items': [{'description': 'Track [SIM_CLK] on B.Cu, length 6.4000 mm', 'pos': {'x': 73.3, 'y': 36.0}}, {'description': 'Track [P0.31] on B.Cu, length 65.3500 mm', 'pos': {'x': 36.75, 'y': 39.5}}]}]",
  "J13_move": "Reverted with P0.31 (atomic)"
}

### P0.22 B-attach geometry (KEPT)
Corridor B@y71.5 col@x109.2. Attach: F-hop VDD_GPIO B@x110.6 at y32.5 → B north to y29.9 @x112.5 → F-hop (112.5→114.7)@y29.9 over P0.04/P0.06 → B into J10.2 PTH. Avoids VDD_GPIO F@y31.08 (pass30q fail mode).

**Backup:** `.mcp-backups/nRF9161-DEV-BOARD.kicad_pcb.pre-pass30r-20260923-122526`  
**DRC:** `reports/DRC_PASS30R_BEFORE.json`, `reports/DRC_PASS30R_MID_P022.json`, `reports/DRC_PASS30R_AFTER.json`  
**Summary:** `reports/PASS30R_SUMMARY.json`

## Pass30s — copper-first P0.31; J13 move only if pad-blocked (2026-09-23 ~12:43 IST)

### Goal
Copper-first corridor for P0.31 (U1.89↔J13.16). **J13 live coords (64,76)→(64,73) only if P0.31 still pad-blocked after copper attempts.** Protect Stage A + pass30i–30r KEEP (incl. P0.22) + P0.15 west wrap + RF/U3. No Gerbers. Never move J11/U1.

### Result
- **Phase:** COMPLETE_PAD_BLOCKED_J13_NOT_KEPT
- **Closed/KEPT:** none
- **Copper-first:** 5 geometries (under-mod B@y34 / B@y33.8 / COEX2 dodge / y30.2 underpass). Closest was v4 (shorting=1 crossing=1: TP9 nRESET pad + COEX2 H@33.2). All reverted.
- **Pad-blocked after copper:** **True** → J13 move gate opened
- **J13 move:** attempted twice (reattach stubs + P0.31 stitch); both **REVERTED** — P0.08 vias @(65.2,72.25)/(65.2,73.95) clearance to J13.1@y73; reattach H corridors mutual crossings (P0.16/17/18)
- **J13 position:** unchanged at **(64.0, 76.0)**
- **P0.31:** still PAD-ONLY (U1.89, J13.16, J11.2)
- **Before/after unconnected:** 69→69 (shorting=0 clearance=0 crossing=0)
- **P0.15 west / Stage A:** preserved

### Blocked
- **P0.31:** No DRC-clean copper corridor without ripping protected copper (COEX2 H@33.2 span x37.75–58.8, VDD2 Stage-A vias, P0.13, TP9/nRESET, J7 SH)
- **J13_move:** Conditionally approved but not keepable with current P0.08 via stack near west end of header

**Backup:** `.mcp-backups/nRF9161-DEV-BOARD.kicad_pcb.pre-pass30s-20260923-123801`  
**DRC:** `reports/DRC_PASS30S_BEFORE.json`, `reports/DRC_PASS30S_MID_COPPER*.json`, `reports/DRC_PASS30S_MID_J13_P031*.json`, `reports/DRC_PASS30S_AFTER.json`  
**Summary:** `reports/PASS30S_SUMMARY.json`

## Pass30t — P0.11 stubs → P0.10/17 → MAGPIO/AUX → VDD_GPIO (2026-09-23 12:50 IST)

### Goal
Copper-only (no placement): P0.11 header stubs → P0.10/P0.17 → MAGPIO/MIPI/AUX if clean → VDD_GPIO islands if low-risk. **SKIP P0.31.** Do NOT rip Stage-A VDD2 / protected wraps. shorting=clearance=crossing=0 or full revert. Protect P0.15 west wrap, RF keepout, U3/matching, P0.22 pass30r keep, pass30i–30r closed copper. Two restore fails → STOP. No Gerbers. No J13/J11 moves.

### Result
- **Phase:** COMPLETE_PARTIAL
- **Closed/KEPT:** ['VDD_GPIO J16↔J17 F-jog@x111.0 (69→68)']
- **Before/after unconnected:** 69→68 (shorting=0 clearance=0 crossing=0)
- **restore_fail_streak:** 0
- **P0.15 west segs:** {'before': 21, 'after': 21, 'preserved': True}
- **Stage A:** {'VDD_nRF_via_north': True, 'VDD2_vias': 2, 'VDD2_present': True}

### Geometry kept
- **VDD_GPIO J16.5↔J17.3:** F east-jog @x=111.0 — (108,31.08)→(111,31.08)→(111,18.16)→(108,18.16). Avoids J17.1 P0.17 @x108/y26 and GND vias @x110.

### Blocked / deferred
- **P0.11_J12_J16:** 4 geometries dirty (B@y9/y6, F@y10, B@x35 F-hops) — ENABLE/VDD1/VDD2/P0.15/P0.01/COEX
- **P0.10:** 2 geometries dirty — ENABLE/VDD2/P0.11/P0.08
- **P0.17:** U1 island + J17 runs dirty — COEX2/P0.08/COEX0/P0.22/P0.01
- **MAGPIO/MIPI:** MAGPIO1 north-band dirty (shorting=8 crossing=12); MIPI same class
- **AUX / AUX_FIT:** RF/GPS clashes; AUX_FIT skipped
- **P0.31:** SKIPPED this pass
- **VDD_GPIO U1.12:** fanout probe dirty — only J16 island kept

### Signal net deltas (excl. GND zone noise)
| Net | Δ unconnected |
| --- | --- |
| VDD_GPIO | -1 |

### GND zone deltas
| Net | Δ |
| --- | --- |
| (none — Class-E skipped) | 0 |

**Backup:** `.mcp-backups/nRF9161-DEV-BOARD.kicad_pcb.pre-pass30t-20260923-124446`  
**DRC:** `reports/DRC_PASS30T_BEFORE.json`, `reports/DRC_PASS30T_MID_*.json`, `reports/DRC_PASS30T_AFTER.json`  
**Summary:** `reports/PASS30T_SUMMARY.json`

## Pass30u — NEW corridors after pass30t KEEP (2026-09-23 12:54 IST)

**Goal:** Close remaining signal opens with NEW corridors; exclude Class-E GND + skip P0.31; avoid exact failed P0.11/P0.10/P0.17 geometries from pass30t.

**Inventory (signal excl GND+P0.31):** VDD_GPIO×3; dual opens P0.05/07/09/10/11/12/17/18/19/21/23/24/30; singles MAGPIO/MIPI/AUX/COEX/SIM/P0.00–29 subset (see `PASS30U_SUMMARY.json` inventory).

| Attempt | Net | Result |
| --- | --- | --- |
| p019_j18_j13_by64 | P0.19 | **KEPT** CLEAN 68→67 (B@y64 + F-hop P0.08) |
| coex0_b_westcol | COEX0 | dirty shorting=6 clearance=4 — reverted |
| p030_j13_j11_east | P0.30 | dirty clearance=1 crossing=7 — reverted |
| vddgpio_mid_bx78 | VDD_GPIO | not attempted (STOP two fails) |
| P0.31 | — | SKIPPED |

**Protect checks:** P0.15 west segs 21→21; Stage A VDD2 vias=2 + VDD_nRF via north OK; P0.22 keep untouched; no Gerbers; no placement.

**Backup:** `.mcp-backups/nRF9161-DEV-BOARD.kicad_pcb.pre-pass30u-20260923-125307`  
**Artifacts:** `reports/DRC_PASS30U_BEFORE.json`, `reports/DRC_PASS30U_AFTER.json`, `reports/PASS30U_SUMMARY.json`, `scripts/final_pass30u.py`

## Pass30v — dual opens NEW corridors after pass30u KEEP (2026-09-23 13:03 IST)

**Goal:** Close dual-open signal nets with NEW corridors in order P0.05→07→09→12→18→21→23→24, then careful VDD_GPIO. SKIP P0.31 / COEX0 / P0.30. Avoid pass30t P0.11/10/17 geometries. shorting=clearance=crossing=0 or revert. Two dirty fails in a row → STOP. Protect Stage A, west wrap, RF/U3, P0.22, P0.19, pass30i–30u copper. No placement. No Gerbers.

**Inventory at start (signal excl GND+P0.31):** VDD_GPIO×3; duals P0.05/07/09/10/11/12/17/18/21/23/24/30; singles MAGPIO/MIPI/AUX/COEX/SIM/P0.* subset.

| Attempt | Net | Result |
| --- | --- | --- |
| p005_j12_j9_fy77 | P0.05 | dirty shorting=10 clearance=3 crossing=14 — reverted |
| p007_j12_j9_fy778 | P0.07 | dirty shorting=10 clearance=1 crossing=10 — reverted |
| (STOP) | — | P0.09/12/18/21/23/24 + VDD_GPIO not attempted |
| P0.31 / COEX0 / P0.30 | — | SKIPPED |

**Post-stop probes (all reverted, not kept):** P0.18/21/23 SE stitches; P0.05 B-west alts; VDD_GPIO mid B@x78. Closest: P0.21v6 short=1 cross=1 (VDD F+B H@y51.08). SE column west of VDD B-wall@x110.6 squeezed by P0.22@109.2 / J17@108 / P0.06@107.4.

**Protect checks:** P0.15 west segs 21→21; Stage A VDD2 vias=2 + VDD_nRF via north OK; P0.22 + P0.19 keep untouched; no Gerbers; no placement.

**Before/after unconnected:** 67→67 (shorting=0 clearance=0 crossing=0)

**Backup:** `.mcp-backups/nRF9161-DEV-BOARD.kicad_pcb.pre-pass30v-20260923-125645`  
**Artifacts:** `reports/DRC_PASS30V_BEFORE.json`, `reports/DRC_PASS30V_AFTER.json`, `reports/PASS30V_SUMMARY.json`, `scripts/final_pass30v.py`

## Pass30x — Placement proposals ONLY (2026-09-23 18:43 IST)

**Goal:** Proposal docs for Hardware PM — coherent placement packages ≤3 mm. **NO** footprint moves, **NO** copper, **NO** Gerbers this pass.

**Board:** untouched (mtime unchanged from pass30w handoff). Live keep = pass30u (unconnected=67).

### PM / DFM override
- **Waive only:** GND ×10 zone islands
- **Must-fix:** ANT_FIT / AUX / AUX_FIT — RF Class C DNP shunt pads (place later under PM OK; never route through RF keepout)
- **Must-fix:** P0.19 / P0.22 leftover ratsnests — real GPIO opens (finish in post-placement copper; Package B primary help)
- **Route-later:** SIM_*, COEX0, GPIO singles (P0.00/01/03/14/16/20/25–29)
- **Hard gate:** unconnected → 0

### Live XY (measured)
| Ref | XY mm | Rot |
| --- | --- | ---: |
| J8 | (50, 6) | 0 |
| J9 | (116, 8) | 0 |
| J10 | (116, 28) | 0 |
| J11 | (116, 46) | 0 |
| J12 | (6, 76) | 90 |
| J13 | (64, 76) | 90 |
| J14 | (104, 48) | 0 |
| J15 | (104, 62) | 0 |
| J16 | (108, 8) | 0 |
| J17 | (108, 26) | 0 |
| U1 | (36, 32) | 180 |

### Packages (summary)
1. **A SE duals** — J16/J9/J17 west 2.54 mm (+ optional J12 east 2.54): unlock P0.05/07/09–12/17
2. **B SE column** — J13 → **(64, 78.5)** preferred / **(67, 76)** alt (avoid failed **(64, 73)** vs P0.08 vias); J10/J11 west 2.54: unlock P0.18–31 + helps finish P0.19/P0.22
3. **C West long-haul** — J14/J15 west 3 mm lockstep: MAGPIO/MIPI/COEX1
4. **D Note only** — VDD_GPIO U1.12 @≈(44, 31.5); **no U1 move** without later explicit OK

**Artifacts:** `reports/PASS30X_PLACEMENT_PROPOSALS.md`, `reports/PASS30X_PLACEMENT_PROPOSALS.json`  
**Next:** Hardware PM approve package(s) → execute placement pass (still no Gerbers until unconnected=0)

## Pass30y — Package B ONLY place+reattach (2026-09-23 18:48 IST)

**Goal:** Execute pass30x Package B (J13+J10+J11) as one atomic package with full reattach of Package B net lists. Preferred J13 (64,78.5); alt once (67,76) only if preferred fails Edge.Cuts/silk/pad clearance toward y=80. shorting=clearance=crossing=0 or full package revert. Protect Stage A, P0.15 west wrap, RF/U3, pass30r/u keeps. No Gerbers. No Package A/C/D. No U1 move.

**Live XY before (measured):** J13(64.0, 76.0) · J10(116.0, 28.0) · J11(116.0, 46.0) · U1(36.0, 32.0)

| Attempt | Landing | Mid DRC | Result |
| --- | --- | --- | --- |
| preferred | J13(64,78.5) J10/J11(113.46,*) | short=11 clr=3 cross=7 hole=4 (edge-class) | reverted → try alt |
| alt (once) | J13(67,76) J10/J11(113.46,*) | short=16 clr=3 cross=4 hole=4 | **full revert** |
| keep | J13(64,76) J10/J11(116,*) | — | pass30u keep restored |

**Blockers (head):**
- Preferred: P0.01 B@y78.5 × P0.18/19/22 stubs; P0.22 via@(112.5,32.5) × J10.3; P0.04 × P0.22 stub; hole_clearance on south pads
- Alt: same J10 west vs P0.22 via@(112.5,32.5); J13.6 P0.21 × P0.01 via@(80.51,76.7); VDD_GPIO F reattach × GND/P0.22

**Protect checks:** P0.15 west preserved; Stage A VDD2 vias + VDD_nRF via north OK; P0.22 + P0.19 copper untouched after revert; U1 unmoved.

**Before/after unconnected:** 67→67 (shorting=0 clearance=0 crossing=0)

**J13 landing kept:** none (both landings dirty)

**Backup:** `.mcp-backups/nRF9161-DEV-BOARD.kicad_pcb.pre-pass30y-20260923-131619` / `.mcp-backups/pass30y-connect/pre-edit.kicad_pcb`  
**Artifacts:** `reports/DRC_PASS30Y_BEFORE.json`, `DRC_PASS30Y_MID_PREF.json`, `DRC_PASS30Y_MID_ALT.json`, `DRC_PASS30Y_AFTER.json`, `reports/PASS30Y_SUMMARY.json`, `reports/PASS30Y_SUMMARY.md`, `scripts/final_pass30y.py`

## Pass30z — RF Class C (C22/C23/C24) — 2026-09-23 13:23 IST

- **Decision:** **KEEP**
- Unconnected **67 → 64**; shorting/clearance/crossing = **0/0/0**
- Class C closed: ANT_FIT, AUX, AUX_FIT (all three)
- Final XY: C22=(17.5, 31.75) rot=-90; C23=(24.8, 34.0); C24=(15.0, 31.8); stubs 0.883 / 1.0 / 1.2 mm; DNP kept
- Details: `reports/PASS30Z_SUMMARY.md` / `.json`; script `scripts/final_pass30z.py`
- Intermediate dirty attempts (C22 on-trunk short; AUX_FIT clearance) reverted before keep

## Pass30aa — Package B' proposals (no execute) — 2026-09-23 IST

- Proposal-only after pass30z KEEP. Preferred: J13(64,75) + J10/J11(115,28)/(115,46); alts in report.
- Banned J13: (64,73), (64,78.5), (67,76). Hard clears: P0.22 via@(112.5,32.5), highways y≈78.5–79.2, P0.01 via@(80.51,76.7).
- Details: `reports/PASS30AA_PACKAGE_B_PROPOSALS.md`

## Pass30ab — Package B' execute (preferred then Alt1-once) — 2026-09-23 18:57 IST

**Goal:** Atomic B' place+reattach. Preferred J13(64,75)+J10/J11(115,*); Alt1 once J13(64,74.5)+J10/J11(115.5,*) if preferred dirty. Gate shorting/clearance/crossing=0 else full revert. Protect Stage A, P0.15 west, RF/U3, pass30r/u, **pass30z Class C**. No Alt2 / Package A / U1 / Gerbers.

| Attempt | Landing | Mid DRC | Result |
| --- | --- | --- | --- |
| preferred | J13(64,75) J10/J11(115,*) | short=4 clr=1 cross=0 | reverted → Alt1 |
| Alt1 (once) | J13(64,74.5) J10/J11(115.5,*) | short=3 clr=2 cross=0 | **full revert** |
| keep | J13(64,76) J10/J11(116,*) | — | pass30z keep restored |

**Blockers (head):** P0.01 F@y74.5 × J13 pads; P0.01 via@(68,74.5); P0.04 F × J11 GND; VDD_GPIO F stubs × J10 P0.22/P0.23; Alt1 also P0.08 via@(65.2,73.95) × J13.1.

**Protect:** Class C C22/C23/C24 stubs+GND vias OK; Stage A OK; P0.15 west OK; U1 unmoved.

**Before/after unconnected:** 64→64 (shorting=clearance=crossing=0/0/0 after revert)

**Landing kept:** none

**Backup:** `.mcp-backups/pass30ab-package-b/pre-edit.kicad_pcb`  
**Artifacts:** `reports/DRC_PASS30AB_{BEFORE,MID_PREF,MID_ALT,AFTER}.json`, `reports/PASS30AB_SUMMARY.{md,json}`, `scripts/final_pass30ab.py`

## Pass30ac — Package A_SE_duals execute (excl J12) — 2026-09-23 13:32 IST

**Goal:** Atomic Package A place+reattach J16+J9+J17. Preferred west −2.54; Alt Y once if dirty. Gate shorting/clearance/crossing=0 else full revert. J12 DO NOT MOVE. SE column FROZEN. Protect Stage A, P0.15 west, RF/U3, pass30r/u, **pass30z Class C**. No Gerbers. No B'' execute.

| Attempt | Landing | Mid DRC | Result |
| --- | --- | --- | --- |
| preferred | J16/J17(105.46,*) J9(113.46,8) | short=7 clr=1 cross=4 | reverted → Alt |
| Alt (once) | J16/J9 y+2.54; J17 y−2.0 | short=11 clr=5 cross=7 unc=68 | **full revert** |
| keep | J16(108,8) J9(116,8) J17(108,26) | — | pass30z keep restored |

**Blockers (head):** Preferred — P0.01 B@y15.2 × J17.3/J16.4; P0.06 × J16.5; P0.04 × J9.6. Alt — VDD_GPIO Y-shift × P0.22 via@(114.7,29.9) / P0.04 via@(113.8,36.8).

**Protect:** Class C C22/C23/C24 OK; Stage A OK; P0.15 west OK; J12/J13/J10/J11/U1 unmoved.

**Before/after unconnected:** 64→64 (shorting=clearance=crossing=0/0/0 after revert)

**Landing kept:** none

**Backup:** `.mcp-backups/pass30ac-package-a/pre-edit.kicad_pcb`  
**Artifacts:** `reports/DRC_PASS30AC_{BEFORE,MID_PREF,MID_ALT,AFTER}.json`, `reports/PASS30AC_SUMMARY.{md,json}`, `scripts/final_pass30ac.py`

## Pass30ad — B'' proposals ONLY (no execute) — 2026-09-23 13:32 IST

- **J10/J11-only:** no safe west ≤3 mm vs P0.22 vias @(112.5,32.5)/(114.7,29.9) + P0.04 F (113.46 banned)
- **Optional J13 west-only ≤2 mm:** (63.5…62.0, 76) statically clear of P0.01/P0.08 forest — does not unlock SE duals alone
- **Recommendation: LEAVE SE COLUMN FROZEN** until copper pre-clear + Hardware PM OK
- No copper execute. No Gerbers.
- Details: `reports/PASS30AD_B_DOUBLE_PRIME_PROPOSALS.md` / `.json`

## Pass30ae — Package C J14/J15 place+reattach — 2026-09-30 03:37 IST

**Goal:** Atomic Package C only. Preferred J14/J15 (101, 48)/(101, 62); alt once (102, 46)/(102, 60). Place+reattach MAGPIO/MIPI/COEX lists. No long-haul through RF keepout. Gate shorting/clearance/crossing=0 else full revert. Frozen SE + east duals, J12, U1, Class C.

| Attempt | Landing | Mid DRC | Result |
| --- | --- | --- | --- |
| preferred | J14/J15 (101, 48)/(101, 62) | short=3 clr=2 cross=0 unc=64 | reverted → alt |
| alt (once) | J14/J15 (102, 46)/(102, 60) | short=11 clr=2 cross=0 unc=64 | **full revert** |
| keep | J14(104, 48) J15(104, 62) | — | pre-edit restored |

**Blockers (head):** Preferred — J14 PTH vs J7 shield GND (MAGPIO1/MAGPIO2) and nRESET B clearance 0.090 mm at x=101.68. Alt — nRESET B shorts MAGPIO0; COEX2 reattach jog shorts J15 GND.

**Protect:** Class C, Stage A, P0.15 west (21), L1/L2/U3, frozen headers all held. No RF-keepout copper added.

**Before/after unconnected:** 64→64 (shorting=clearance=crossing=0/0/0 after revert)

**Landing kept:** none

**Backup:** `.mcp-backups/pass30ae-package-c/pre-edit.kicad_pcb`  
**Artifacts:** `reports/DRC_PASS30AE_{BEFORE,MID_PREF,MID_ALT,AFTER}.json`, `reports/PASS30AE_SUMMARY.{md,json}`, `scripts/final_pass30ae.py`

## Pass30af — SIM_RST_C preclear (after AE revert) — 2026-09-30 03:42 IST

**Decision:** **KEEP** one net only. P0.04 / P0.06 / P0.01 and the P0.22 keep were not ripped (closed GPIO or explicit keep). SE column x>108 unchanged.

**Edit:** Deleted two dangling duplicate `SIM_RST_C` B tracks `(79.38, 44.60)–(97.30, 44.60)`. Jogged the live B trunk to y=45.00 and trimmed the via risers so they no longer tail into y=44.60.

**Corridor freed (not routed):** B.Cu y≈44.60, x≈81.8–97.3, for one 0.18 mm signal between `SIM_CLK_C` @y44.05 and the jogged trunk.

**Unconnected:** 64→64 (delta 0). shorting/clearance/crossing=0/0/0. track_dangling 15→13.

**Backup:** `.mcp-backups/pass30af-preclear/pre-edit.kicad_pcb`  
**Artifacts:** `reports/PASS30AF_PRECLEAR_PLAN.{md,json}`, `reports/DRC_PASS30AF_{BEFORE,MID_SIM_RST_C,AFTER}.json`, `reports/PASS30AF_SUMMARY.{md,json}`, `scripts/final_pass30af_preclear.py`

## Pass30ag — one signal in the B.Cu y=44.60 corridor — 2026-09-30 03:49 IST

**Decision:** **REVERT**. Net attempted: `SIM_RST`. SIM_RST_C was already continuous (0 opens), so the corridor was spare.

**Attempt:** one 0.18 mm B.Cu segment (81.80, 44.60)–(97.30, 44.60) only. No header move. No Class C / P0.22 / frozen east-SE rip.

**Why it does not close a net:** the slot is a sealed pocket (not a clearance collision). Mid DRC on the probe was short/clearance/crossing = 0/0/0, but unconnected rose 64→65 because the segment touched no SIM_RST island. West mouth is walled by `SIM_IO_C` B @ x=78.60 and `SIM_CLK_C` B @ x=78.95; east mouth by `SIM_CLK_C` B @ x=97.85. No open SIM_* or GPIO island pair both touches that centerline.

**Unconnected:** 64→64. short/clearance/crossing after REVERT: 0/0/0. Corridor still free.

**Artifacts:** `reports/PASS30AG_SUMMARY.md`, `reports/PASS30AG_SUMMARY.json`, `reports/DRC_PASS30AG_BEFORE.json`, `reports/DRC_PASS30AG_MID_SIM_RST.json`, `reports/DRC_PASS30AG_AFTER.json`, `scripts/final_pass30ag.py`

## Pass30aj — VDD_GPIO to U1.12, one shove (2026-09-30 IST)

**Decision:** **REVERT**. Path: **shove** (west not attempted — the shove does not enter the P0.15 keep). The pass30ai east spine at x=45.5 was not repeated. Straight line not used.

**Edit (reverted):** 0.18 mm F.Cu polyline (40.170, 19.126)→(40.170, 20.200)→(45.900, 20.200)→(45.900, 25.400)→(47.550, 25.400)→(47.550, 31.500)→(44.000, 31.500). Shoved only P0.12 and P0.10 (dangling vias 47.4→47.0) and DEC0 (F gap around x=47.55 bridged on B.Cu; dangling via parked at (45.40, 30.55)). P0.08 and P0.11 not on this polyline, not shoved. P0.15 segments 42→42.

**Gate:** short/clearance/crossing/hole_clearance = 0/0/0/0. VDD_GPIO opens 3→2 (U1.12 was reached) but a new F.Cu GND zone island (10→11) offset it, so headline unconnected stayed 64→64. The 186 mm² F.Cu GND pour (stitch via @(50, 10)) is split by any F exit from the via island. Full byte restore.

**Unconnected:** 64→64. **GND islands:** 10→10 after revert.

**Artifacts:** `reports/DRC_PASS30AJ_{BEFORE,MID,AFTER}.json`, `reports/PASS30AJ_SUMMARY.{md,json}`, `scripts/final_pass30aj.py`, backup `.mcp-backups/pass30aj/pre-edit.kicad_pcb`

## Pass30ak — replay pass30aj VDD_GPIO shove, GND islands waived — 2026-09-30 10:05 IST

**Decision:** **KEEP**. Exact replay of `scripts/final_pass30aj.py` (`apply_shove` + `add_poly`). Not a new corridor. West not attempted. x=45.5 spine not used.

**Edit:** 0.18 mm F.Cu polyline (40.170, 19.126)→(40.170, 20.200)→(45.900, 20.200)→(45.900, 25.400)→(47.550, 25.400)→(47.550, 31.500)→(44.000, 31.500). Shoved only P0.12 and P0.10 dangling vias (47.4, 27.5)/(47.4, 28.5) → (47.0, 27.5)/(47.0, 28.5). DEC0: F.Cu gap around the VDD drop at x=47.55, B.Cu bridge (46.950, 30.900)–(48.100, 30.900), dangling via parked at (45.400, 30.550). P0.08 and P0.11 not on this polyline, not shoved. P0.15 segments 42→42.

**Gate (GND islands waived):** short/clearance/crossing/hole_clearance = 0/0/0/0. VDD_GPIO opens 3→2. No non-GND net gained an open. The extra F.Cu GND zone island (10→11) is waived and was not a revert reason. Copper diff vs pre-edit touches only DEC0, P0.10, P0.12, and VDD_GPIO. Footprints unchanged (U1 stays at (36, 32)).

**Unconnected:** 64→64. **VDD_GPIO opens:** 3→2. **GND islands:** 10→11 (waived).

**Artifacts:** `reports/DRC_PASS30AK_{BEFORE,MID,AFTER}.json`, `reports/PASS30AK_SUMMARY.{md,json}`, `scripts/final_pass30ak.py`, backup `.mcp-backups/pass30ak/pre-edit.kicad_pcb`

## Pass30ao — island remeasure, no qualifying gap — 2026-09-30 10:37 IST

**Decision:** **NO-ROUTE**. No copper. No backup. Board bytes unchanged.

**Live remeasure** (`reports/DRC_PASS30AO_BEFORE.json`, island copper matches DRC opens): unconnected 63, VDD_GPIO opens 1, GND islands 12 (ignored for ranking), short/clearance/crossing/hole_clearance 0/0/0, hole_to_hole 1.

**Priority 1:** the remaining VDD_GPIO open is **27.034 mm** on F.Cu, pad U2.5 (74.519, 39.306) ↔ pad J18.9 (58.859, 61.343). Over the 25 mm cap, so it was not closed. The locked y=7.050 path was not repeated.

**Priority 2:** shortest other non-GND gap is `P0.31` **29.078 mm**, over the 20 mm cap. No other non-GND pair is ≤ 20 mm.

**POWER clearance:** not measured — no track was added.

**Five shortest non-GND gaps:** VDD_GPIO 27.034, P0.31 29.078, P0.30 32.207, P0.14 34.038, P0.16 34.259. Detail: `reports/PASS30AO_SHORTLIST.md`.

**Protect:** locked VDD_GPIO (y=7.050 and the U1.12 polyline), COEX0, DEC0 bridge, P0.10/P0.12 vias, P0.15 west wrap, Class C, P0.22, P0.19, Stage-A VDD2, SIM walls, y=44.60 pocket, RF keepout, U1 and headers all untouched. No Gerbers. No git commit.

**Artifacts:** `reports/PASS30AO_SUMMARY.{md,json}`, `reports/PASS30AO_SHORTLIST.{md,json}`, `reports/DRC_PASS30AO_BEFORE.json`, `scripts/final_pass30ao.py`

## Pass30ap — last VDD_GPIO open, jog around ENABLE / SIM_CLK / P0.20 — 2026-09-30 10:47 IST

**Decision:** **KEEP**. No new via. Width 0.18 mm. Segments 8.

Straight F.Cu U2.5→J18.9 not used. Jog: existing via (76.4375, 39.050) south/west around ENABLE and SIM_CLK, then to x=54.438 west of the P0.20 trunk, south, into J18.9.

**POWER clearance:** 2.2373 mm (≥ 0.20). **VDD_GPIO opens:** 1→0. **Unconnected:** 63→62. **GND islands:** 12→12 (waived).

**Artifacts:** `reports/PASS30AP_SUMMARY.{md,json}`, `reports/DRC_PASS30AP_{BEFORE,MID,AFTER}.json`, `scripts/final_pass30ap.py`

## Pass30aq — P0.31 jog around P0.22 / P0.04 / VDD_GPIO — 2026-09-30 11:01 IST

**Decision:** **KEEP**. No via. Width 0.18 mm. Segments 6.

Straight F.Cu J13.16→J11.2 not used. Jog: (102.60, 75.50) on J13.16, x=103.05 west of J14 to y=47.10, east to x=106.70, y=50.62 north of VDD_GPIO and south of the P0.04 corner, east to x=114.90, into J11.2 at (115.55, 48.80).

**Foreign clearance:** 0.23 mm (≥ 0.15). **POWER clearance:** 0.245 mm (≥ 0.20). **P0.31 opens:** 2→1. **Unconnected:** 62→61. **GND islands:** 12→12 (waived).

**Artifacts:** `reports/PASS30AQ_SUMMARY.{md,json}`, `reports/DRC_PASS30AQ_{BEFORE,MID,AFTER}.json`, `scripts/final_pass30aq.py`

## Pass30ar — P0.31 U1.89 leftover, no route — 2026-09-30 11:07 IST

**Decision:** **NO-ROUTE**. No copper. No backup. No via.

The remaining P0.31 open is pad U1.89, alone, to the locked pass30aq island. Pad-edge gap **66.737 mm** on F.Cu: pad U1.89 (36.900, 37.614) to the west edge of F.Cu (103.05, 47.10)–(106.70, 47.10) at (102.961, 47.087). Over 25 mm, so the one jog was not attempted.

A straight 0.18 mm line between those endpoints overlaps locked and foreign copper (nearest SIM_CLK via@(70.9, 42.4) at -0.301 mm; also VDD2, SIM_CLK_C, VDD_GPIO, P0.04, COEX0). It was not used. The six-segment P0.31 run was not ripped. P0.30 was not started.

**Five shortest non-GND opens:** P0.30 32.207, P0.14 34.038, P0.16 34.259, P0.17 34.863, P0.18 35.644. The U1.89 leftover at 66.737 mm is recorded with them. Detail: `reports/PASS30AR_SHORTLIST.md`.

**Unconnected:** 61→61. **P0.31 opens:** 1→1.

**Artifacts:** `reports/PASS30AR_SUMMARY.{md,json}`, `reports/PASS30AR_SHORTLIST.{md,json}`

## Pass30as — P0.30 header-to-header jog — 2026-09-30 11:23 IST

**Decision:** **KEEP**. Via yes (112.40, 46.40) od 0.60 drill 0.30. Width 0.18 mm. Segments 8.

Straight F.Cu J13.15→J11.1 not used. F.Cu: (99.56, 75.28) on J13.15, y=74.70, x=101.20 west of locked P0.31, y=46.40, via (112.40, 46.40). B.Cu: y=45.00 east gutter x=117.60 into J11.1 at (116.70, 46.00).

**Foreign clearance:** 0.29 mm (≥ 0.15). **POWER clearance:** 0.7 mm (≥ 0.20). **P0.30 opens:** 2→1. **Unconnected:** 61→60. **GND islands:** 12→12 (waived).

**Artifacts:** `reports/PASS30AS_SUMMARY.{md,json}`, `reports/DRC_PASS30AS_{BEFORE,MID,AFTER}.json`, `scripts/final_pass30as.py`

## Pass30at — P0.30 U1.88 leftover, no route — 2026-09-30 11:27 IST

**Decision:** **NO-ROUTE**. No copper. No backup. No via.

The remaining P0.30 open is pad U1.88, with via (36.250, 41.100), to the locked pass30as island (J13.15 / J11.1). Copper-edge gap **64.776 mm** on F.Cu: via ring (36.549, 41.124) to the west edge of F.Cu (101.20, 46.40)–(112.40, 46.40) at (101.110, 46.393). U1.88 pad-edge to that track is 65.303 mm. Over 25 mm, so the one jog was not attempted.

A straight 0.18 mm line between those endpoints overlaps locked and foreign copper (nearest SIM_1V8 F.Cu (75.52, 44.00)–(75.52, 46.00) at -0.290 mm; also VDD2, VDD_GPIO, COEX0, SIM_CLK_C). It was not used. The eight-segment P0.30 run was not ripped. P0.31 U1.89 was not retried. P0.14 was not started.

**Five shortest connector-to-connector opens:** P0.24 49.625, P0.23 53.192, P0.18 59.678, P0.21 59.990, P0.17 62.907. The U1.88 leftover at 64.776 mm is recorded with them and is not a candidate. Detail: `reports/PASS30AT_SHORTLIST.md`.

**Unconnected:** 60→60. **P0.30 opens:** 1→1.

**Artifacts:** `reports/PASS30AT_SUMMARY.{md,json}`, `reports/PASS30AT_SHORTLIST.{md,json}`

## Pass30au — P0.14 around the SiP, no route — 2026-09-30 11:45 IST

**Decision:** **NO-ROUTE**. No copper. No via. No backup. The 25 mm cap was waived for this net and the straight line was still not used.

**Remeasured gap:** 34.038 mm on F.Cu, pad J18.2 island (40.623, 61.154) ↔ pad U1.24 (42.136, 27.15). P0.14 opens 1→1. Ratsnest edges 60→60.

**Straight line:** crosses the SiP body and the south fanout. Worst hits include GND -0.336 mm (via@42.0,29.0); P0.04 -0.168 mm (F.Cu (41.25,46.80)-(37.40,46.80)); P0.03 -0.156 mm (via@41.75,41.1); <no-net> -0.09 mm (pad U1.127 (no net)). Not used.

**Blocker:** U1.24's F.Cu pocket is closed. Pad gaps to P0.13/P0.15 are 0.2 / 0.2 mm (need 0.48 mm). North via pinch copper gap 0.4 mm (need 0.48 mm). B.Cu in the pocket is GND fill; the halo beside P0.13 is 0.25 mm and will not take a via. No east-of-package jog within 8 segments and one via without entering the body, the south fanout, or the pour. Locked copper not ripped. U1.88 / U1.89 not retried. P0.24 not started. No Gerbers.

**Artifacts:** `reports/PASS30AU_SUMMARY.{md,json}`, `scripts/final_pass30au.py`

## Pass30av — P0.14 via in the pocket, revert — 2026-09-30 12:06 IST

**Decision:** **REVERT**. One via at (42.25, 25.50), 0.50/0.30, plus one F.Cu stub (42.25, 26.40)–(42.25, 25.50). Refill cleared the via: True (B.Cu pad-edge 0.2505 mm). B.Cu segments 0. The free B.Cu component from the via is x 29.0–46.2, y 16.0–26.6 and does not reach J18.2, so no 8-segment route was added.

**Clearance of the new copper (mid, after refill):** foreign 0.16 mm, POWER 0.702 mm, hole-to-hole 1.3286 mm.

**P0.14 opens:** 1 → 1 (mid 1). **Unconnected:** 60 → 60 (mid 60). GND islands waived. Full restore to `.mcp-backups/pass30av/pre-edit.kicad_pcb`. No F.Cu pinch retry. P0.13/P0.15 vias not moved. U1.88 / U1.89 not retried. P0.24 not started. No Gerbers. No git commit.

**Artifacts:** `reports/PASS30AV_SUMMARY.{md,json}`, `reports/DRC_PASS30AV_BEFORE.json`, `reports/DRC_PASS30AV_MID.json`, `reports/DRC_PASS30AV_AFTER.json`, `scripts/final_pass30av.py`

## Pass30ay — P0.17 north-exit jog — 2026-09-30 12:57 IST

**Decision:** **KEEP**. In2.Cu 0.18 mm, no new via: (40.25, 23.10)→(40.25, 21.50)→(45.55, 21.50)→(45.55, 27.40)→(44.60, 27.40)→(44.60, 60.40)→(48.16, 60.40)→(48.16, 61.30).

Remeasured pad-edge U1.28↔J18.5 **34.860 mm** (effective shapes; chord between (40.378, 27.147) and (47.913, 61.187) is 34.864 mm). Foreign 0.21 mm vs {'net': 'P0.06', 'item': 'via@45.150,36.000'}. POWER 0.3378 mm vs {'net': 'VDD2', 'item': 'via@44.722,25.900'}. Straight 0.18 mm F.Cu chord (40.378, 27.147)→(47.913, 61.187) not used (crosses the SiP; GND via (42.0, 35.0)). F.Cu and B.Cu free space from via (40.25, 23.10) die at y=26.5. Existing through-via kept. No second via. Locked P0.16 In1 skirt not ripped. x>24.2. No header or U1 move. No Gerbers. No commit.

**P0.17 opens:** 2 → 1. **Unconnected:** 59 → 58. **short/clearance/crossing/hole:** 0/0/0/0. **hole_to_hole:** 1 → 1. **GND islands:** 12 → 12 (waived).

**Artifacts:** `reports/PASS30AY_SUMMARY.md`, `reports/PASS30AY_SUMMARY.json`, `reports/DRC_PASS30AY_BEFORE.json`, `reports/DRC_PASS30AY_MID.json`, `reports/DRC_PASS30AY_AFTER.json`, `scripts/final_pass30ay.py`

## Pass30az — P0.17 J17.1 leftover, no route — 2026-09-30 13:09 IST

**Decision:** **NO-ROUTE**. No copper. No via. No backup. Stopping rule: length. Pad-edge **61.510 mm** on In2.Cu (limit 36 mm). Endpoints: J17.1 (108.000, 26.000), PTH on F.Cu/In1.Cu/In2.Cu/B.Cu; and the pass30ay In2.Cu track (45.550, 21.500)–(45.550, 27.400) on the island with U1.28 (40.250, 26.750) F.Cu, J18.5 (48.160, 62.000), J13.2 (66.540, 76.000). Not a south U1 pad and not J10/J11.

Straight 0.18 mm chord (45.640, 26.000)→(107.150, 26.000) does not cross the SiP fab body. Foreign under 0.15 mm: 5. POWER/VIN under 0.20 mm: 3. Chord not used. Skirt not ripped. P0.19 and P0.20 not started. Unconnected 58→58. P0.17 opens 1→1. No other net touched. No Gerbers. No commit.

**Artifacts:** `reports/PASS30AZ_SUMMARY.md`, `reports/PASS30AZ_SUMMARY.json`, `scripts/final_pass30az.py`

## Pass30ba — P0.19 — 2026-09-30 13:23 IST

**Decision:** **NO-ROUTE**. U1.30 and J18.7 were separate (pad-edge 36.658 mm). One In1.Cu 8-segment jog from via (39.25, 23.10) to J18.7 was added and fully restored: the eastbound (44.25, 60.00)–(53.24, 60.00) crosses the locked P0.16 skirt (44.60, 27.40)–(44.60, 60.40) at (44.60, 60.00), so mid DRC was short/clearance/crossing/hole 0/0/1/0 even though P0.19 opens went 1→0 and unconnected 58→57. Straight F.Cu chord (39.378, 27.147)→(52.993, 61.187) crosses the SiP and hits VDD1 at −0.29 mm on (50.52, 38.00)–(43.25, 38.00); not used. F.Cu and B.Cu die at y=26.5. POWER pre-add 0.274 mm vs VDD2 via (44.722, 25.900). Post-revert unconnected 58, P0.19 opens 1, hole_to_hole 1, GND islands 12. Skirts not ripped. P0.17 not retried. No other net. No Gerbers. No commit.

## Pass30bb — P0.19 — 2026-09-30 13:32 IST

**Decision:** **KEEP**. Kept In1.Cu 0.18 mm, no new via: (39.25, 23.10)→(39.25, 26.50)→(44.25, 26.50)→(44.25, 39.10)→(42.80, 39.90)→(44.25, 40.70)→(44.25, 63.20)→(53.24, 63.20)→(53.24, 62.00). Whole-segment test against both skirts (intersection plus 0.05 mm samples, layers not exempt) found 0 crossings; min centerline distance 0.35 mm. y=61.63 was not used: it clears the end caps and hits J18.4 (0.0 mm). Eastbound y=63.20 is south of both end caps and the 1.7 mm pads, then north onto J18.7, not past it. Foreign 0.17 mm vs {'net': 'P0.16', 'item': 'trk (44.60,27.40)-(44.60,60.40)'}. POWER 0.2736 mm vs {'net': 'VDD2', 'item': 'via@44.722,25.900'}. P0.19 opens 1→0. Unconnected 58→57. short/clearance/crossing/hole 0/0/0/0. hole_to_hole 1→1. GND islands 12→12 (waived). Skirts not crossed or ripped. P0.17 not retried. No other net. No Gerbers. No commit.

## Pass30bc — P0.20 — 2026-09-30 13:43 IST

**Decision:** **KEEP**. Kept In2.Cu 0.18 mm, no new via: (36.20, 20.80)→(36.45, 20.80)→(36.45, 26.50)→(44.25, 26.50)→(44.25, 39.10)→(42.80, 39.90)→(44.25, 40.70)→(44.25, 63.20)→(55.78, 63.20)→(55.78, 62.00). Ends were already one island: False. Far island layers: ['F.Cu', 'In1.Cu', 'In2.Cu', 'B.Cu']. Pad-edge 38.594909 mm. Straight chord hit P0.06 at -0.3726 mm and crosses the body; not used. Whole-segment test crossings 0; min center to P0.16/P0.17 0.35 mm. Foreign 0.17 mm vs {'net': 'P0.17', 'item': 'trk (44.60,27.40)-(44.60,60.40)'}. POWER 0.2736 mm vs {'net': 'VDD2', 'item': 'via@44.722,25.900'}. P0.20 opens 1→0. Unconnected 57→56. short/clearance/crossing/hole 0/0/0/0. hole_to_hole 1→1. GND islands 12→12 (waived). No third In1 skirt. No via punched into an F.Cu-only pad. Skirts and P0.19 not ripped. No other net. No Gerbers. No commit.

## Pass30bd — SIM_CLK — 2026-09-30 13:58 IST

**Decision:** **KEEP**. Ends already one island: False. Pad-edge 40.989923 mm (census 40.990). Straight F.Cu chord crosses the body and hits VDD2 (61.3, 42.0) at -0.4185 mm; not used. x=44.93 remeasured at -0.12 mm to P0.06; x=43.92 is inside the body. Skirt slot was not the only way and was not used. Kept In1.Cu 0.18 mm, 9 segments, no new via, north of the four skirts then south at x=57.20 onto via (73.30, 36.00). Foreign 0.169 mm vs {'net': 'ENABLE', 'item': 'via@56.500,20.300'}. POWER 0.2836 mm vs {'net': 'VDD_GPIO', 'item': 'via@40.170,19.126'}. SIM_CLK opens 1→0. Unconnected 56→55. short/clearance/crossing/hole 0/0/0/0. hole_to_hole 1. GND islands 12→12 (waived). Whole-segment crossings 0. Skirts not ripped or stacked. No other net. No Gerbers. No commit.

## Pass30be — SIM_RST — 2026-09-30 17:18 IST

**Decision:** **KEEP**. Pad-edge 42.124496 mm (census 42.124). P0.25 flank at x=32.71 remeasured 0.15 mm (exact 0.150, not under 0.15); that x was not used as a through-run because it crosses SIM_CLK In1 at (32.71, 22.665). Straight F.Cu chord hits VDD1 (50.68, 35)-(50.68, 31) at -0.29 mm; not used. Kept 9 segments (1 F.Cu + 8 In1.Cu) and one 0.50/0.30 through-via at (32.75, 25.50), landing on existing through-via (78.00, 36.00). Foreign 0.16 mm vs {'net': 'COEX0', 'item': 'B.Cu trk (32.25,22.00)-(32.25,30.50)'}. POWER 0.2358 mm vs {'net': 'VDD1', 'item': 'via@49.438,16.874'}. SIM_RST opens 1→0. Unconnected 55→54. short/clearance/crossing/hole 0/0/0/0. hole_to_hole 1. GND islands 12→12 (waived). Four skirts and the SIM_CLK run not ripped or stacked. No other net. No Gerbers. No commit.

## Pass30bf — P0.00 — 2026-09-30 17:28 IST

**Decision:** **KEEP**. Pad-edge 43.297995 mm (census 43.298). Via (39.75, 41.10) on U1.95 island: True (pad 0.6 mm, drill 0.3 mm). Far layers ['F.Cu', 'In1.Cu', 'In2.Cu', 'B.Cu']; through-vias [{'name': 'via@80.140,19.126', 'xy': [80.14, 19.125833], 'width_mm': 0.6, 'drill_mm': 0.3, 'nm': [80140000, 19125833]}]. Straight F.Cu chord hits VDD1 (50.68, 35)-(50.68, 31); not used. Kept 9 In1.Cu segments, no new via, from via (39.75, 41.10) to via (80.14, 19.125833). Foreign 0.16 mm vs {'net': 'MIPI_VIO', 'item': 'via@24.650,24.400'}. POWER 0.2457 mm vs {'net': 'VDD2', 'item': 'via@68.137,16.874'}. Whole-segment crossings 0. P0.00 opens 1→0. Unconnected 54→53. short/clearance/crossing/hole 0/0/0/0. hole_to_hole 1. GND islands 12→12 (waived). SIM_RST, SIM_CLK, and the four skirts not ripped or stacked. Skirt slot and sealed pocket not used. No other net. No Gerbers. No commit.

## Pass30bg — P0.07 — 2026-09-30 17:41 IST

**Decision:** **KEEP**. Pad-edge 44.117219 mm (census 44.118). Named via (47.40, 36.50) on U1.4 island: False (net P0.05; not used). P0.07 via (47.40, 35.50) on U1.4 island: True (pad 0.6 mm, drill 0.3 mm). J12.8 center [23.78, 76.0]; layers ['F.Cu', 'In1.Cu', 'In2.Cu', 'B.Cu']. Straight F.Cu chord hits P0.02 via (40.75, 41.10) at -0.215 mm; not used. Kept 9 In2.Cu segments, no new via, from via (47.40, 35.50) onto J12.8. Foreign 0.18 mm vs {'net': 'P0.08', 'item': 'pad J12.9'}. POWER 0.2842 mm vs {'net': 'VDD2', 'item': 'via@59.700,37.126'}. Whole-segment crossings 0. P0.07 opens 2→1. Unconnected 53→52. short/clearance/crossing/hole 0/0/0/0. hole_to_hole 1. GND islands 12→12 (waived). P0.00, SIM_RST, SIM_CLK, and the four skirts not ripped or stacked. Skirt slot, sealed pocket, and RF keepout not used. No other net. No Gerbers. No commit.

## Pass30bh — P0.07 J9.2 leftover, no route — 2026-09-30 17:47 IST

**Decision:** **NO-ROUTE**. No copper. No via. No backup. Stopping rule: length. Pad-edge **58.616524 mm** on In2.Cu (limit 36 mm, over the cap). Leftover pad J9.2 center (116.000, 10.540), circular PTH, copper on F.Cu, In1.Cu, In2.Cu, B.Cu. Nearest closed-island copper is the locked In2 round cap at (63.10, 37.90), track-edge (63.180, 37.859) to pad-edge (115.245, 10.930). Closed U1.4/J12.8 run not ripped and not stacked. P0.00, SIM_RST, SIM_CLK, and the four skirts not touched. P0.05 via (47.40, 36.50) still P0.05; not routed. Unconnected 52→52. P0.07 opens 1→1. short/clearance/crossing/hole 0/0/0/0. hole_to_hole 1. GND islands 12. No other net. No Gerbers. No commit.

## Pass30bi — P0.05 U1.2 to J12.6 — 2026-09-30 18:00 IST

**Decision:** **KEEP**. Pad-edge 45.730103 mm (census 45.733). Via (47.40, 36.50) on U1.2 island: True (pad 0.6 mm, drill 0.3 mm, net P0.05). J12.6 center [18.7, 76.0]; size [1.7, 1.7] mm; drill 1.0 mm; layers ['F.Cu', 'In1.Cu', 'In2.Cu', 'B.Cu']. Straight F.Cu chord hits P0.02 via (40.75, 41.10) at -0.353 mm; not used. Other P0.05 opens left: [{'name': 'J9.3', 'xy': [116.0, 13.08], 'island': ['J9.3'], 'same_as_u1': False, 'same_as_j12': False}]. Kept 7 In1.Cu segments, no new via, from via (47.40, 36.50) onto J12.6 from the south. Foreign 0.33 mm vs {'net': 'P0.20', 'item': 'pad J18.8'}. POWER 0.33 mm vs {'net': 'VDD_GPIO', 'item': 'pad J18.9'}. Whole-segment crossings 0. P0.05 opens 2→1. U1.2↔J12.6 open True→False. Unconnected 52→51. short/clearance/crossing/hole 0/0/0/0. hole_to_hole 1. GND islands 12→12 (waived). P0.07, P0.00, SIM_RST, SIM_CLK, and the four skirts not ripped or stacked. J9.2 not touched. Skirt slot, sealed pocket, and RF keepout not used. No other net. No Gerbers. No commit.

## Pass30bj — P0.05 J9.3 leftover, no route — 2026-09-30 18:05 IST

**Decision:** **NO-ROUTE**. No copper. No via. No backup. Stopping rule: length. Pad-edge **63.217656 mm** on In1.Cu (limit 36 mm, over the cap). Leftover pad J9.3 center (116.000, 13.080), circle PTH 1.700 mm, drill 1.000 mm, copper on F.Cu, In1.Cu, In2.Cu, B.Cu. Nearest closed-island copper is the locked In1 round cap at (57.05, 38.40), track-edge (57.133, 38.364) to pad-edge (115.219, 13.415). Closed U1.2/J12.6 run not ripped and not stacked. P0.07, P0.00, SIM_RST, SIM_CLK, and the four skirts not touched. J9.2 still P0.07 at [116.0, 10.54]; not touched, stays open. Unconnected 51→51. P0.05 opens 1→1. short/clearance/crossing/hole 0/0/0/0. hole_to_hole 1. GND islands 12. No other net. No Gerbers. No commit.
