anand2532/nRF9161-DEV-BOARD/scripts/final_pass30al.py

#!/usr/bin/env python3
"""pass30al — ONE attempt: close COEX0 (R4 island -> south F.Cu island).

Straight F.Cu from the y=22 island to the y=38 run hits no-net pads U1.51
and U1.73. Pad pitch is 0.50 mm with 0.30 mm pads (0.20 mm gaps); a 0.18 mm
track at 0.10 mm clearance cannot pass between them. A west F.Cu jog that
stays x>24.2 crosses MAGPIO/MIPI fanout and the ANT/AUX/GPS matching
(AUX horizontal reaches x=20.485). The west corridor also cannot hold a via.
One via is required to land.

Route (6 segments, 0.18 mm, one 0.6/0.3 via), all x>24.2:
  B (31.110,22.000)->(32.250,22.000)->(32.250,30.500)->(37.000,30.500)
  via (37.000,30.500)
  F (37.000,30.500)->(37.000,35.900)->(38.750,35.900)->(38.750,37.250)
Lands on U1.93 / the existing COEX0 F.Cu vertical, which is the same island
as the (26.20,38)-(33.00,38) run. Does not take the straight line.

KEEP if COEX0 opens drop, no other non-GND net gains an open, and
short/clearance/crossing/hole_clearance are 0. Extra GND zone island is
waived. hole_to_hole must not increase. Else FULL REVERT.
"""
from __future__ import annotations

import hashlib
import json
import re
import shutil
import subprocess
from collections import Counter
from datetime import datetime
from pathlib import Path
from zoneinfo import ZoneInfo

import pcbnew

ROOT = Path("/workspace/kicad-projects/nRF9161-DEV-BOARD")
BOARD = ROOT / "nRF9161-DEV-BOARD.kicad_pcb"
BACKUP = ROOT / ".mcp-backups/pass30al/pre-edit.kicad_pcb"
REPORTS = ROOT / "reports"
REVIEW = ROOT / "docs/PCB_LAYOUT_REVIEW.md"
F = pcbnew.F_Cu
B = pcbnew.B_Cu
W = 0.18

B_POLY = [
    (31.110, 22.000),
    (32.250, 22.000),
    (32.250, 30.500),
    (37.000, 30.500),
]
F_POLY = [
    (37.000, 30.500),
    (37.000, 35.900),
    (38.750, 35.900),
    (38.750, 37.250),
]
VIA = (37.000, 30.500)

VDD_POLY = [
    (40.170, 19.126),
    (40.170, 20.200),
    (45.900, 20.200),
    (45.900, 25.400),
    (47.550, 25.400),
    (47.550, 31.500),
    (44.000, 31.500),
]


def ist_now() -> str:
    return datetime.now(ZoneInfo("Asia/Kolkata")).strftime("%Y-%m-%d %H:%M IST")


def mm(v) -> float:
    return pcbnew.ToMM(v)


def xy(x, y):
    return pcbnew.VECTOR2I(pcbnew.FromMM(x), pcbnew.FromMM(y))


def near(a, b, tol=0.02) -> bool:
    return abs(a - b) < tol


def sha(p) -> str:
    return hashlib.sha256(Path(p).read_bytes()).hexdigest()


def ends(t):
    return (mm(t.GetStart().x), mm(t.GetStart().y), mm(t.GetEnd().x), mm(t.GetEnd().y))


def track_is(t, x1, y1, x2, y2) -> bool:
    a, b, c, d = ends(t)
    return (near(a, x1) and near(b, y1) and near(c, x2) and near(d, y2)) or (
        near(a, x2) and near(b, y2) and near(c, x1) and near(d, y1)
    )


def add_track(board, net, layer, x1, y1, x2, y2):
    t = pcbnew.PCB_TRACK(board)
    t.SetStart(xy(x1, y1))
    t.SetEnd(xy(x2, y2))
    t.SetWidth(pcbnew.FromMM(W))
    t.SetLayer(layer)
    t.SetNet(net)
    board.Add(t)
    return t


def add_via(board, net, x, y):
    v = pcbnew.PCB_VIA(board)
    v.SetPosition(xy(x, y))
    v.SetWidth(F, pcbnew.FromMM(0.6))
    v.SetWidth(B, pcbnew.FromMM(0.6))
    v.SetDrill(pcbnew.FromMM(0.3))
    v.SetViaType(pcbnew.VIATYPE_THROUGH)
    v.SetNet(net)
    board.Add(v)
    return v


def p015_count(board) -> int:
    return sum(
        1
        for t in board.GetTracks()
        if t.GetNetname() == "P0.15" and t.GetClass() != "PCB_VIA"
    )


def vdd_poly_ok(board) -> bool:
    tracks = [
        t
        for t in board.GetTracks()
        if t.GetClass() != "PCB_VIA" and t.GetNetname() == "VDD_GPIO" and t.GetLayer() == F
    ]
    for (x1, y1), (x2, y2) in zip(VDD_POLY, VDD_POLY[1:]):
        if not any(track_is(t, x1, y1, x2, y2) and abs(mm(t.GetWidth()) - W) < 0.001 for t in tracks):
            return False
    return True


def dec0_bridge_ok(board) -> bool:
    for t in board.GetTracks():
        if t.GetNetname() == "DEC0" and t.GetLayer() == B and track_is(t, 46.950, 30.900, 48.100, 30.900):
            return True
    return False


def footprint_xy(board) -> dict:
    out = {}
    for f in board.GetFootprints():
        out[f.GetReference()] = (
            round(mm(f.GetPosition().x), 4),
            round(mm(f.GetPosition().y), 4),
            round(f.GetOrientationDegrees(), 3),
        )
    return out


def confirm(board) -> dict:
    vias = []
    tracks = []
    for t in board.GetTracks():
        if t.GetNetname() != "COEX0":
            continue
        if t.GetClass() == "PCB_VIA":
            vias.append(
                {
                    "x": round(mm(t.GetPosition().x), 3),
                    "y": round(mm(t.GetPosition().y), 3),
                    "dia": round(mm(t.GetWidth(F)), 3),
                    "drill": round(mm(t.GetDrill()), 3),
                }
            )
        elif t.GetLayer() == F:
            a, b, c, d = ends(t)
            tracks.append(
                {
                    "start": [round(a, 3), round(b, 3)],
                    "end": [round(c, 3), round(d, 3)],
                    "w": round(mm(t.GetWidth()), 3),
                }
            )
    u1 = next(f for f in board.GetFootprints() if f.GetReference() == "U1")
    pads = {}
    for num in ("51", "73", "93"):
        p = next(p for p in u1.Pads() if p.GetNumber() == num)
        pads[num] = {
            "net": p.GetNetname(),
            "x": round(mm(p.GetPosition().x), 3),
            "y": round(mm(p.GetPosition().y), 3),
            "size": [round(mm(p.GetSize().x), 3), round(mm(p.GetSize().y), 3)],
        }
    r4 = next(f for f in board.GetFootprints() if f.GetReference() == "R4")
    r4p = next(p for p in r4.Pads() if p.GetNumber() == "1")
    info = {
        "u1": {"x": round(mm(u1.GetPosition().x), 3), "y": round(mm(u1.GetPosition().y), 3)},
        "pads": pads,
        "r4_1": {
            "net": r4p.GetNetname(),
            "x": round(mm(r4p.GetPosition().x), 3),
            "y": round(mm(r4p.GetPosition().y), 3),
        },
        "coex0_vias": vias,
        "coex0_f_tracks": tracks,
        "p015": p015_count(board),
        "vdd_poly": vdd_poly_ok(board),
        "dec0_bridge": dec0_bridge_ok(board),
    }
    return info


def nongnd_counts(data) -> Counter:
    c: Counter = Counter()
    for it in data.get("unconnected_items", []):
        desc = " ".join(i.get("description", "") for i in it.get("items", []))
        nets = {n for n in re.findall(r"\[([^\]]+)\]", desc) if n != "GND"}
        for n in nets:
            c[n] += 1
    return c


def gnd_items(data) -> int:
    n = 0
    for it in data.get("unconnected_items", []):
        desc = " ".join(i.get("description", "") for i in it.get("items", []))
        if "[GND]" in desc:
            n += 1
    return n


def run_drc(dest: Path) -> dict:
    tmp = Path("/tmp/nrf30al_drc.json")
    subprocess.check_call(
        ["kicad-cli", "pcb", "drc", "--format", "json", "--output", str(tmp), str(BOARD)],
        stdout=subprocess.DEVNULL,
        stderr=subprocess.DEVNULL,
    )
    shutil.copy2(tmp, dest)
    data = json.loads(dest.read_text())
    vc = Counter(v["type"] for v in data.get("violations", []))
    stats = {
        "unconnected_items": len(data.get("unconnected_items", [])),
        "shorting_items": vc.get("shorting_items", 0),
        "clearance": vc.get("clearance", 0),
        "tracks_crossing": vc.get("tracks_crossing", 0),
        "hole_clearance": vc.get("hole_clearance", 0),
        "hole_to_hole": vc.get("hole_to_hole", 0),
        "gnd_zone_islands": gnd_items(data),
        "coex0_unconnected": nongnd_counts(data).get("COEX0", 0),
        "via_dangling": vc.get("via_dangling", 0),
        "track_dangling": vc.get("track_dangling", 0),
    }
    return {"stats": stats, "data": data}


def apply_route(board):
    net = board.FindNet("COEX0")
    if net is None:
        raise SystemExit("COEX0 net missing")
    for (x1, y1), (x2, y2) in zip(B_POLY, B_POLY[1:]):
        add_track(board, net, B, x1, y1, x2, y2)
    add_via(board, net, *VIA)
    for (x1, y1), (x2, y2) in zip(F_POLY, F_POLY[1:]):
        add_track(board, net, F, x1, y1, x2, y2)


def segment_rows():
    rows = []
    for (x1, y1), (x2, y2) in zip(B_POLY, B_POLY[1:]):
        rows.append({"layer": "B.Cu", "width_mm": W, "start": [x1, y1], "end": [x2, y2]})
    for (x1, y1), (x2, y2) in zip(F_POLY, F_POLY[1:]):
        rows.append({"layer": "F.Cu", "width_mm": W, "start": [x1, y1], "end": [x2, y2]})
    return rows


def write_outputs(decision, info, before_stats, after_stats, gained, reason, keep):
    ts = ist_now()
    segs = segment_rows()
    payload = {
        "pass": "30al",
        "timestamp": ts,
        "decision": decision,
        "net": "COEX0",
        "via_used": True,
        "via": {"x": VIA[0], "y": VIA[1], "dia": 0.6, "drill": 0.3},
        "straight_line": False,
        "why_not_straight": "F.Cu straight line hits no-net pads U1.51 (28.750,26.750) and U1.73 (28.750,37.250)",
        "why_not_west_fcu_jog": (
            "West of the package and east of x=24.2, F.Cu crosses MAGPIO1/MAGPIO2/MIPI_VIO/"
            "MIPI_SCLK and ANT/AUX/GPS. AUX horizontal reaches x=20.485, so no southbound "
            "F.Cu exists with x>24.2. Pad pitch 0.50 mm cannot be threaded. A via does not "
            "fit in the west corridor beside MAGPIO2."
        ),
        "segments": segs,
        "segment_count": len(segs),
        "confirmed": info,
        "before": before_stats,
        "after": after_stats,
        "coex0_opens": {
            "before": before_stats.get("coex0_unconnected"),
            "after": after_stats.get("coex0_unconnected"),
        },
        "headline_unconnected": {
            "before": before_stats.get("unconnected_items"),
            "after": after_stats.get("unconnected_items"),
        },
        "gnd_islands": {
            "before": before_stats.get("gnd_zone_islands"),
            "after": after_stats.get("gnd_zone_islands"),
            "waived": True,
        },
        "nongnd_gained": gained,
        "hole_to_hole": {
            "before": before_stats.get("hole_to_hole"),
            "after": after_stats.get("hole_to_hole"),
        },
        "gate_met": keep,
        "reason": reason,
        "protect": {
            "vdd_gpio_polyline": info.get("vdd_poly_after", info.get("vdd_poly")),
            "dec0_bcu_bridge": info.get("dec0_after", info.get("dec0_bridge")),
            "p015_segments": {
                "before": info.get("p015"),
                "after": info.get("p015_after", info.get("p015")),
            },
            "u1_unmoved": True,
            "headers_unmoved": True,
            "y_44_60_pocket": "not used",
            "x_gt_24_2": True,
            "gerbers": False,
            "git_commit": False,
        },
    }
    (REPORTS / "PASS30AL_SUMMARY.json").write_text(json.dumps(payload, indent=2) + "\n")

    def row(s):
        return (
            f"| {s['layer']} | ({s['start'][0]:.3f}, {s['start'][1]:.3f}) | "
            f"({s['end'][0]:.3f}, {s['end'][1]:.3f}) | {s['width_mm']:.2f} mm |"
        )

    b = before_stats
    a = after_stats
    lines = [
        "# PASS30AL_SUMMARY — COEX0 landing (GND islands waived)",
        "",
        f"**Timestamp:** {ts}",
        "**KiCad:** 9.0.2",
        f"**Decision:** **{decision}**",
        "**Net:** COEX0",
        f"**Via:** yes — through via (37.000, 30.500) dia 0.6 drill 0.3",
        f"**Segments:** {len(segs)} (limit 6)",
        f"**Unconnected:** {b.get('unconnected_items')} → {a.get('unconnected_items')}",
        f"**COEX0 opens:** {b.get('coex0_unconnected')} → {a.get('coex0_unconnected')}",
        f"**GND zone islands:** {b.get('gnd_zone_islands')} → {a.get('gnd_zone_islands')} (increase WAIVED)",
        "",
        "## Why not the straight line",
        "",
        "Live islands: F.Cu COEX0 (26.200, 38.000)–(33.000, 38.000) and the R4.1 island",
        "via (29.810, 22.000) / (31.110, 22.000). A straight F.Cu drop near x=28.75 hits",
        "no-net pads U1.51 (28.750, 26.750) and U1.73 (28.750, 37.250), both 0.30×0.80.",
        "North/south pad pitch is 0.50 mm, so the gap between pads is 0.20 mm — a 0.18 mm",
        "track at 0.10 mm clearance does not fit. The route does not take that line.",
        "",
        "A west F.Cu jog staying x>24.2 cannot land either: it crosses MAGPIO1, MAGPIO2,",
        "MIPI_VIO, MIPI_SCLK and the ANT/AUX/GPS matching tracks. AUX on F.Cu runs to",
        "x=20.485, west of the x=24.2 keepout, so there is no southbound F.Cu east of",
        "x=24.2. A via does not fit in the remaining west corridor beside MAGPIO2",
        "(hole-to-copper). One via is used so the jog can land.",
        "",
        "## Confirmed live coordinates",
        "",
        f"- U1 @ ({info['u1']['x']}, {info['u1']['y']}) unmoved",
        f"- U1.51 net={info['pads']['51']['net']!r} ({info['pads']['51']['x']}, {info['pads']['51']['y']}) size {info['pads']['51']['size']}",
        f"- U1.73 net={info['pads']['73']['net']!r} ({info['pads']['73']['x']}, {info['pads']['73']['y']}) size {info['pads']['73']['size']}",
        f"- U1.93 net={info['pads']['93']['net']!r} ({info['pads']['93']['x']}, {info['pads']['93']['y']}) size {info['pads']['93']['size']}",
        f"- R4.1 net={info['r4_1']['net']!r} ({info['r4_1']['x']}, {info['r4_1']['y']})",
        f"- P0.15 segments before {info.get('p015')} after {info.get('p015_after', info.get('p015'))}",
        f"- VDD_GPIO polyline present: {info.get('vdd_poly_after', info.get('vdd_poly'))}",
        f"- DEC0 B.Cu bridge present: {info.get('dec0_after', info.get('dec0_bridge'))}",
        "",
        "## Path",
        "",
        "Not the straight line. Not a west F.Cu wrap (it cannot clear RF matching and stay",
        "x>24.2). Existing north via (31.110, 22.000) is already on the R4 island, so the",
        "route leaves on B.Cu, passes east of U1.51/U1.73 inside the module via field,",
        "and returns to F.Cu beside the thermal pads to land on U1.93, which is the same",
        "island as the y=38 F.Cu run. P0.15 west wrap (x=41.75) is not touched.",
        "Minimum x on this route is 31.110 (>24.2). Maximum y is 37.250 (the y=44.60",
        "B.Cu pocket is not used).",
        "",
        f"Reason: {reason}",
        "",
        "### Segments (0.18 mm)",
        "",
        "| layer | start | end | width |",
        "| --- | --- | --- | --- |",
    ]
    for s in segs:
        lines.append(row(s))
    lines += [
        "",
        f"Via: (37.000, 30.500) through, dia 0.60 mm, drill 0.30 mm, net COEX0.",
        "",
        "## Gate (GND islands waived)",
        "",
        f"- short/clear/cross/hole_clearance all zero: "
        f"{a.get('shorting_items')==0 and a.get('clearance')==0 and a.get('tracks_crossing')==0 and a.get('hole_clearance')==0}",
        f"- COEX0 opens drop: {b.get('coex0_unconnected')} → {a.get('coex0_unconnected')}",
        f"- no non-GND net gained an open: {not gained} {gained or ''}",
        f"- hole_to_hole did not increase: {b.get('hole_to_hole')} → {a.get('hole_to_hole')}",
        f"- GND islands: WAIVED ({b.get('gnd_zone_islands')} → {a.get('gnd_zone_islands')})",
        f"- **met: {keep}**",
        "",
        "## DRC",
        "",
        "| | unconnected | shorting | clearance | tracks_crossing | hole_clearance | hole_to_hole | GND islands | COEX0 opens |",
        "| --- | ---: | ---: | ---: | ---: | ---: | ---: | ---: | ---: |",
        f"| before | {b.get('unconnected_items')} | {b.get('shorting_items')} | {b.get('clearance')} | {b.get('tracks_crossing')} | {b.get('hole_clearance')} | {b.get('hole_to_hole')} | {b.get('gnd_zone_islands')} | {b.get('coex0_unconnected')} |",
        f"| after ({decision}) | {a.get('unconnected_items')} | {a.get('shorting_items')} | {a.get('clearance')} | {a.get('tracks_crossing')} | {a.get('hole_clearance')} | {a.get('hole_to_hole')} | {a.get('gnd_zone_islands')} | {a.get('coex0_unconnected')} |",
        "",
        "## Protect checklist",
        "",
        "- VDD_GPIO F.Cu polyline locked and still present",
        "- P0.10 and P0.12 vias at x=47.0 not moved",
        "- DEC0 B.Cu bridge (46.950, 30.900)–(48.100, 30.900) not ripped",
        f"- P0.15 west wrap segment count {info.get('p015')} → {info.get('p015_after', info.get('p015'))}",
        "- Class C C22/C23/C24, P0.22, P0.19, Stage-A VDD2, SIM_IO_C/SIM_CLK_C walls not ripped",
        "- No U1 or header move",
        "- y=44.60 B.Cu pocket not used",
        "- RF keepout: this route stays east of x=24.2 (min x=31.110); no new digital under the matching network",
        "- No Gerbers. No git commit.",
        "",
    ]
    (REPORTS / "PASS30AL_SUMMARY.md").write_text("\n".join(lines))
    return ts


def patch_review(ts, decision, before_stats, after_stats):
    text = REVIEW.read_text()
    b, a = before_stats, after_stats
    banner = (
        f"**Review date:** {ts} (Asia/Calcutta) — pass30al COEX0 "
        f"{'KEEP' if decision=='KEEP' else 'REVERT'} "
        f"(unc {b.get('unconnected_items')}→{a.get('unconnected_items')}; "
        f"COEX0 opens {b.get('coex0_unconnected')}→{a.get('coex0_unconnected')}; "
        f"GND islands {b.get('gnd_zone_islands')}→{a.get('gnd_zone_islands')}). "
    )
    # replace the review-date sentence prefix only
    old = text.split("— pass30ak", 1)
    if len(old) == 2:
        head = old[0]
        # head ends with the date clause start; keep from 'Prior:'
        rest = old[1]
        prior = rest.split("Prior:", 1)
        if len(prior) == 2:
            text = (
                banner
                + "Prior: pass30ak VDD_GPIO shove KEEP. Prior:"
                + prior[1]
            )
            # The banner replaced the whole line start including '**Review date:**'
            # but head still contains the old review date line up to '— pass30ak'.
            # Rebuild properly:
            pre, _sep, _post = REVIEW.read_text().partition("**Review date:**")
            after_prior = REVIEW.read_text().split("Prior:", 1)[1]
            text = (
                pre
                + banner
                + "Prior: pass30ak VDD_GPIO shove KEEP (unc headline was 64; VDD_GPIO opens 3→2; GND island 10→11 waived). Prior:"
                + after_prior
            )
    delta = (
        f"**Pass delta (pass30al):** COEX0 landing, **{decision}**. Straight F.Cu from the "
        f"R4 via island (29.810, 22.000) to the y=38 run hits no-net U1.51 and U1.73; "
        f"0.50 mm pad pitch cannot be threaded, and a west F.Cu jog east of x=24.2 crosses "
        f"MAGPIO/MIPI and ANT/AUX/GPS (AUX reaches x=20.485). One 0.6/0.3 via at "
        f"(37.000, 30.500). Six 0.18 mm segments: B (31.110, 22.000)→(32.250, 22.000)→"
        f"(32.250, 30.500)→(37.000, 30.500), F (37.000, 30.500)→(37.000, 35.900)→"
        f"(38.750, 35.900)→(38.750, 37.250) onto U1.93 (same island as the y=38 run). "
        f"COEX0 opens {b.get('coex0_unconnected')}→{a.get('coex0_unconnected')}. "
        f"Headline unconnected {b.get('unconnected_items')}→{a.get('unconnected_items')}. "
        f"short/clearance/crossing/hole_clearance "
        f"{a.get('shorting_items')}/{a.get('clearance')}/{a.get('tracks_crossing')}/{a.get('hole_clearance')}. "
        f"hole_to_hole {b.get('hole_to_hole')}→{a.get('hole_to_hole')}. "
        f"GND islands {b.get('gnd_zone_islands')}→{a.get('gnd_zone_islands')} (waived). "
        f"No non-GND net gained an open. P0.15 still 42. VDD_GPIO polyline, DEC0 B.Cu bridge, "
        f"P0.10/P0.12 x=47.0 not ripped. No U1/header move. No y=44.60 pocket. No Gerbers. "
        f"Details: `reports/PASS30AL_SUMMARY.md`.\n\n"
    )
    needle = "**Pass delta (pass30ak):**"
    if needle not in text:
        raise SystemExit("review doc anchor missing")
    text = text.replace(needle, delta + needle, 1)
    # connectivity headline row
    text = text.replace(
        "| **unconnected_items** | **64** | `reports/DRC_PASS30AK_AFTER.json` (live `kicad-cli` 9.0.2). Headline unchanged: VDD_GPIO opens 3→2, one extra F.Cu GND zone island 10→11 waived. Prior pass30ac/pass30z Class C + Stage A + P0.22/P0.19 kept",
        f"| **unconnected_items** | **{a.get('unconnected_items')}** | `reports/DRC_PASS30AL_AFTER.json` (live `kicad-cli` 9.0.2). COEX0 opens {b.get('coex0_unconnected')}→{a.get('coex0_unconnected')}. GND islands {b.get('gnd_zone_islands')}→{a.get('gnd_zone_islands')}. Prior pass30ak VDD_GPIO kept",
    )
    if decision == "KEEP":
        text = text.replace(
            "| **shorting_items** | **0** | `reports/DRC_PASS30AK_AFTER.json` |",
            "| **shorting_items** | **0** | `reports/DRC_PASS30AL_AFTER.json` |",
        )
    REVIEW.write_text(text)


def main():
    BACKUP.parent.mkdir(parents=True, exist_ok=True)
    REPORTS.mkdir(parents=True, exist_ok=True)
    if BACKUP.is_file():
        if sha(BOARD) != sha(BACKUP):
            raise SystemExit(
                "pass30al backup exists and the live board does not match it; "
                "refusing to clobber the pre-edit or double-apply"
            )
    else:
        shutil.copy2(BOARD, BACKUP)
    if sha(BOARD) != sha(BACKUP):
        raise SystemExit("backup hash mismatch before edit")

    print("BACKUP", sha(BACKUP))
    before = run_drc(REPORTS / "DRC_PASS30AL_BEFORE.json")
    print("BEFORE", before["stats"])

    board = pcbnew.LoadBoard(str(BOARD))
    info = confirm(board)
    print("CONFIRM", json.dumps({k: info[k] for k in ("u1", "pads", "r4_1", "p015", "vdd_poly", "dec0_bridge")}))
    if info["p015"] != 42 or not info["vdd_poly"] or not info["dec0_bridge"]:
        raise SystemExit(f"protect confirm failed: {info['p015']} vdd={info['vdd_poly']} dec0={info['dec0_bridge']}")
    if info["u1"]["x"] != 36.0 or info["u1"]["y"] != 32.0:
        raise SystemExit("U1 moved before edit; refusing")
    p51, p73 = info["pads"]["51"], info["pads"]["73"]
    if p51["net"] != "" or not near(p51["x"], 28.75, 0.02) or not near(p51["y"], 26.75, 0.02):
        raise SystemExit(f"U1.51 not where expected: {p51}")
    if p73["net"] != "" or not near(p73["x"], 28.75, 0.02) or not near(p73["y"], 37.25, 0.02):
        raise SystemExit(f"U1.73 not where expected: {p73}")
    if info["pads"]["93"]["net"] != "COEX0":
        raise SystemExit("U1.93 is not COEX0")
    north = [v for v in info["coex0_vias"] if near(v["x"], 31.110, 0.02) and near(v["y"], 22.000, 0.02)]
    if not north:
        raise SystemExit("north COEX0 via (31.110, 22.000) missing")
    fp_before = footprint_xy(board)

    apply_route(board)
    p015_after = p015_count(board)
    vdd_after = vdd_poly_ok(board)
    dec0_after = dec0_bridge_ok(board)
    fp_after = footprint_xy(board)
    moved = sorted(ref for ref in fp_before if fp_before[ref] != fp_after.get(ref))
    info["p015_after"] = p015_after
    info["vdd_poly_after"] = vdd_after
    info["dec0_after"] = dec0_after
    if p015_after != 42 or not vdd_after or not dec0_after or moved:
        print("ABORT", p015_after, vdd_after, dec0_after, moved)
        shutil.copy2(BACKUP, BOARD)
        after = run_drc(REPORTS / "DRC_PASS30AL_AFTER.json")
        write_outputs(
            "REVERT",
            info,
            before["stats"],
            after["stats"],
            {},
            f"geometry guard failed p015={p015_after} vdd={vdd_after} dec0={dec0_after} moved={moved}",
            False,
        )
        return

    pcbnew.ZONE_FILLER(board).Fill(board.Zones())
    pcbnew.SaveBoard(str(BOARD), board)

    mid = run_drc(REPORTS / "DRC_PASS30AL_MID.json")
    print("MID", mid["stats"])
    gained = {}
    bc = nongnd_counts(before["data"])
    ac = nongnd_counts(mid["data"])
    for n in set(ac) | set(bc):
        if ac[n] > bc[n]:
            gained[n] = {"before": bc[n], "after": ac[n]}
    st = mid["stats"]
    bst = before["stats"]
    electrical = (
        st["coex0_unconnected"] < bst["coex0_unconnected"]
        and not gained
        and st["shorting_items"] == 0
        and st["clearance"] == 0
        and st["tracks_crossing"] == 0
        and st["hole_clearance"] == 0
        and st["hole_to_hole"] <= bst["hole_to_hole"]
    )
    if electrical:
        shutil.copy2(REPORTS / "DRC_PASS30AL_MID.json", REPORTS / "DRC_PASS30AL_AFTER.json")
        reason = (
            "COEX0 open closed without a new short, clearance, crossing, or hole hit. "
            "Straight F.Cu was not used. One via because a west F.Cu jog cannot land."
        )
        ts = write_outputs("KEEP", info, bst, st, gained, reason, True)
        patch_review(ts, "KEEP", bst, st)
        print("KEEP", st)
    else:
        shutil.copy2(BACKUP, BOARD)
        after = run_drc(REPORTS / "DRC_PASS30AL_AFTER.json")
        reason = (
            f"gate failed coex {bst['coex0_unconnected']}->{st['coex0_unconnected']} "
            f"gained={gained} short={st['shorting_items']} clr={st['clearance']} "
            f"cross={st['tracks_crossing']} hole={st['hole_clearance']} "
            f"h2h {bst['hole_to_hole']}->{st['hole_to_hole']}"
        )
        # after revert, report the reverted (clean) stats as after, and the failed mid in reason
        ts = write_outputs("REVERT", info, bst, after["stats"], gained, reason, False)
        patch_review(ts, "REVERT", bst, after["stats"])
        print("REVERT", reason)


if __name__ == "__main__":
    main()
