anand2532/nRF9161-DEV-BOARD/scripts/final_pass30ao.py

#!/usr/bin/env python3
"""pass30ao — remeasure live island gaps. No copper unless a qualifying gap exists.

Priority:
  1. Remaining VDD_GPIO open (exactly one after pass30an) if its copper gap is <= 25 mm.
  2. Else the shortest other non-GND gap that is <= 20 mm.
  3. Else NO-ROUTE. Write the five shortest non-GND gaps and stop.

This run is the no-route branch. The script refuses to place copper. If a later
board state would qualify, it aborts instead of writing a false NO-ROUTE.
GND zone islands are ignored when ranking. Protected keeps are measured but
only appear in the five if they are actually among the shortest non-GND gaps.
"""
from __future__ import annotations

import hashlib
import json
import shutil
import subprocess
import sys
from collections import Counter
from datetime import datetime
from pathlib import Path
from zoneinfo import ZoneInfo

import pcbnew

sys.path.insert(0, str(Path(__file__).resolve().parent))
import final_pass30ah as ah  # noqa: E402

ROOT = Path("/workspace/kicad-projects/nRF9161-DEV-BOARD")
BOARD = ROOT / "nRF9161-DEV-BOARD.kicad_pcb"
REPORTS = ROOT / "reports"
REVIEW = ROOT / "docs/PCB_LAYOUT_REVIEW.md"
BEFORE = REPORTS / "DRC_PASS30AO_BEFORE.json"
VDD_CAP = 25.0
OTHER_CAP = 20.0


def ist_now() -> str:
    return datetime.now(ZoneInfo("Asia/Kolkata")).strftime("%Y-%m-%d %H:%M IST")


def sha(p: Path) -> str:
    return hashlib.sha256(p.read_bytes()).hexdigest()


def load_open_nets(data):
    return ah.load_open_nets_from(data)


def drc_stats(data) -> dict:
    vc = Counter(v["type"] for v in data.get("violations", []))
    opens = load_open_nets(data)
    return {
        "unconnected_items": len(data.get("unconnected_items", [])),
        "shorting_items": vc.get("shorting_items", 0),
        "clearance": vc.get("clearance", 0),
        "tracks_crossing": vc.get("tracks_crossing", 0),
        "hole_clearance": vc.get("hole_clearance", 0),
        "hole_to_hole": vc.get("hole_to_hole", 0),
        "gnd_zone_islands": opens.get("GND", 0),
        "vdd_gpio_unconnected": opens.get("VDD_GPIO", 0),
    }


def run_drc() -> dict:
    tmp = Path("/tmp/nrf30ao_drc.json")
    subprocess.check_call(
        ["kicad-cli", "pcb", "drc", "--format", "json", "--output", str(tmp), str(BOARD)],
        stdout=subprocess.DEVNULL,
        stderr=subprocess.DEVNULL,
    )
    shutil.copy2(tmp, BEFORE)
    return json.loads(BEFORE.read_text())


def all_gaps(board, opens):
    """Every non-GND island pair, including protected keeps, shortest first."""
    by = ah.collect(board)
    ah.add_nonet(board, by)
    rows = []
    audit = {}
    for net, nopen in opens.items():
        if net == "GND":
            audit[net] = {"skip": "gnd zone islands", "drc_opens": nopen}
            continue
        prims = by.get(net, [])
        if not prims:
            audit[net] = {"skip": "no copper", "drc_opens": nopen}
            continue
        islands = ah.cluster(prims)
        audit[net] = {
            "drc_opens": nopen,
            "islands": len(islands),
            "prims": len(prims),
            "protected": net in ah.PROTECTED_NETS,
            "islands_match_drc": len(islands) == nopen + 1,
        }
        if len(islands) < 2:
            continue
        for a in range(len(islands)):
            for b in range(a + 1, len(islands)):
                best, same = ah.best_gap(prims, islands[a], islands[b])
                if best is None:
                    continue
                g, pa, pb, pi, pj, shared = best
                layer = None
                sp = sq = None
                sg = None
                if same:
                    sg, sp, sq, spi, spj, _ = same
                    layer = next(iter(spi.layers & spj.layers))
                blocks = ah.line_blocks(by, net, sp, sq, layer) if same else []
                rows.append(
                    {
                        "net": net,
                        "protected_keep": net in ah.PROTECTED_NETS,
                        "gap_mm": round(g, 3),
                        "closest_a": [ah.r3(pa[0]), ah.r3(pa[1])],
                        "closest_b": [ah.r3(pb[0]), ah.r3(pb[1])],
                        "a_item": pi.label,
                        "b_item": pj.label,
                        "a_layers": sorted(ah.LAYER_NAME[l] for l in pi.layers),
                        "b_layers": sorted(ah.LAYER_NAME[l] for l in pj.layers),
                        "same_layer_gap_mm": None if sg is None else round(sg, 3),
                        "same_layer": None if layer is None else ah.LAYER_NAME[layer],
                        "same_a": None if sp is None else [ah.r3(sp[0]), ah.r3(sp[1])],
                        "same_b": None if sq is None else [ah.r3(sq[0]), ah.r3(sq[1])],
                        "island_a": ah.island_summary(prims, islands[a]),
                        "island_b": ah.island_summary(prims, islands[b]),
                        "straight_blocks": blocks,
                        "corridor": ah.corridor_hit(sp, sq, layer) if same else False,
                        "rf_keepout": ah.rf_keepout_hit(
                            sp if sp else pa, sq if sq else pb, layer if layer is not None else ah.F
                        ),
                        "via_possible": g <= 0.60,
                    }
                )
    rows.sort(key=lambda r: r["gap_mm"])
    return rows, audit


def fmt_pt(p):
    return f"({p[0]:.3f}, {p[1]:.3f})"


def layers_of(names):
    return "+".join(names) if names else "?"


def gate_blocker(r, vdd_gap):
    """Why this pair is not the pass30ao route."""
    bits = []
    if r["net"] == "VDD_GPIO":
        bits.append(
            f"remaining VDD_GPIO open is {r['gap_mm']:.3f} mm, over the 25 mm cap, so priority 1 does not qualify"
        )
    else:
        bits.append(
            f"{r['gap_mm']:.3f} mm is over the 20 mm cap for any non-VDD_GPIO gap "
            f"(remaining VDD_GPIO is {vdd_gap:.3f} mm, already over 25 mm)"
        )
    bits.append(ah.why_blocked(r))
    if r["protected_keep"]:
        bits.append("net is a locked keep; a join that ripped that copper would not be placed")
    return "; ".join(bits)


def write_reports(rows, audit, stats, stamp, board_sha):
    vdd = [r for r in rows if r["net"] == "VDD_GPIO"]
    if len(vdd) != 1:
        raise SystemExit(f"expected exactly one VDD_GPIO gap, found {len(vdd)}")
    vdd_gap = vdd[0]["gap_mm"]
    others = [r for r in rows if r["net"] != "VDD_GPIO"]
    if not others:
        raise SystemExit("no other non-GND gaps")
    other_min = others[0]
    if not (vdd_gap > VDD_CAP and other_min["gap_mm"] > OTHER_CAP):
        raise SystemExit(
            f"qualifying gap appeared (VDD_GPIO {vdd_gap} mm, "
            f"shortest other {other_min['net']} {other_min['gap_mm']} mm). "
            "This script must not place copper and must not claim NO-ROUTE."
        )
    mismatched = [
        net
        for net, info in audit.items()
        if net != "GND" and "islands" in info and not info["islands_match_drc"]
    ]
    if mismatched:
        raise SystemExit(f"island count does not match DRC opens: {mismatched}")

    five = rows[:5]
    short_rows = []
    for i, r in enumerate(five, 1):
        short_rows.append(
            {
                "rank": i,
                "net": r["net"],
                "distance_mm": r["gap_mm"],
                "protected_keep": r["protected_keep"],
                "island_a": {
                    "closest_copper_mm": r["closest_a"],
                    "layers": r["a_layers"],
                    "item": r["a_item"],
                    "pads": r["island_a"]["pads"],
                    "anchor_mm": r["island_a"]["anchor"],
                    "island_layers": r["island_a"]["layers"],
                    "primitives": r["island_a"]["n"],
                },
                "island_b": {
                    "closest_copper_mm": r["closest_b"],
                    "layers": r["b_layers"],
                    "item": r["b_item"],
                    "pads": r["island_b"]["pads"],
                    "anchor_mm": r["island_b"]["anchor"],
                    "island_layers": r["island_b"]["layers"],
                    "primitives": r["island_b"]["n"],
                },
                "same_layer": r["same_layer"],
                "same_layer_gap_mm": r["same_layer_gap_mm"],
                "blocker": gate_blocker(r, vdd_gap),
            }
        )

    summary = {
        "pass": "30ao",
        "timestamp": stamp,
        "decision": "NO-ROUTE",
        "routed": False,
        "net": None,
        "distance_mm": vdd_gap,
        "vdd_gpio_remaining_gap_mm": vdd_gap,
        "vdd_gpio_cap_mm": VDD_CAP,
        "vdd_gpio_qualifies": False,
        "shortest_other_net": other_min["net"],
        "shortest_other_gap_mm": other_min["gap_mm"],
        "other_cap_mm": OTHER_CAP,
        "other_qualifies": False,
        "why": (
            f"Remaining VDD_GPIO open is {vdd_gap:.3f} mm (>{VDD_CAP:.0f} mm) between "
            f"F.Cu pad U2.5 {fmt_pt(vdd[0]['closest_a'])} and pad J18.9 {fmt_pt(vdd[0]['closest_b'])}. "
            f"Shortest other non-GND gap is {other_min['net']} {other_min['gap_mm']:.3f} mm "
            f"(>{OTHER_CAP:.0f} mm). Neither priority qualifies, so no track and no via."
        ),
        "path": None,
        "via_used": False,
        "segments": [],
        "power_clearance_measured_mm": None,
        "power_clearance_note": "No copper placed, so POWER/VIN clearance was not measured against a new track.",
        "unconnected_before": stats["unconnected_items"],
        "unconnected_after": stats["unconnected_items"],
        "vdd_gpio_opens_before": stats["vdd_gpio_unconnected"],
        "vdd_gpio_opens_after": stats["vdd_gpio_unconnected"],
        "gnd_islands_before": stats["gnd_zone_islands"],
        "gnd_islands_after": stats["gnd_zone_islands"],
        "gnd_islands_waived": True,
        "shorting_items": stats["shorting_items"],
        "clearance": stats["clearance"],
        "tracks_crossing": stats["tracks_crossing"],
        "hole_clearance": stats["hole_clearance"],
        "hole_to_hole": stats["hole_to_hole"],
        "board_sha256": board_sha,
        "board_modified": False,
        "backup": None,
        "drc_before": "reports/DRC_PASS30AO_BEFORE.json",
        "drc_mid": None,
        "drc_after": None,
        "island_audit_matches_drc": True,
        "y_7_050_path_not_repeated": True,
        "y_44_60_pocket_not_used": True,
        "locked_copper_not_ripped": True,
        "no_gerbers": True,
        "no_git_commit": True,
        "five": [{"net": s["net"], "distance_mm": s["distance_mm"]} for s in short_rows],
    }
    shortlist = {
        "pass": "30ao",
        "timestamp": stamp,
        "decision": "NO-ROUTE",
        "rule": (
            "Do not route. Priority 1 needs the remaining VDD_GPIO gap <= 25 mm. "
            "Priority 2 needs some other non-GND gap <= 20 mm. Neither is true on the live board. "
            "GND zone islands ignored."
        ),
        "vdd_gpio_remaining_gap_mm": vdd_gap,
        "shortest_other": {"net": other_min["net"], "distance_mm": other_min["gap_mm"]},
        "five": short_rows,
    }
    (REPORTS / "PASS30AO_SUMMARY.json").write_text(json.dumps(summary, indent=2) + "\n")
    (REPORTS / "PASS30AO_SHORTLIST.json").write_text(json.dumps(shortlist, indent=2) + "\n")
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
